cscott/3d-track60/roundabout-stl/roundabout-8-outer.stl

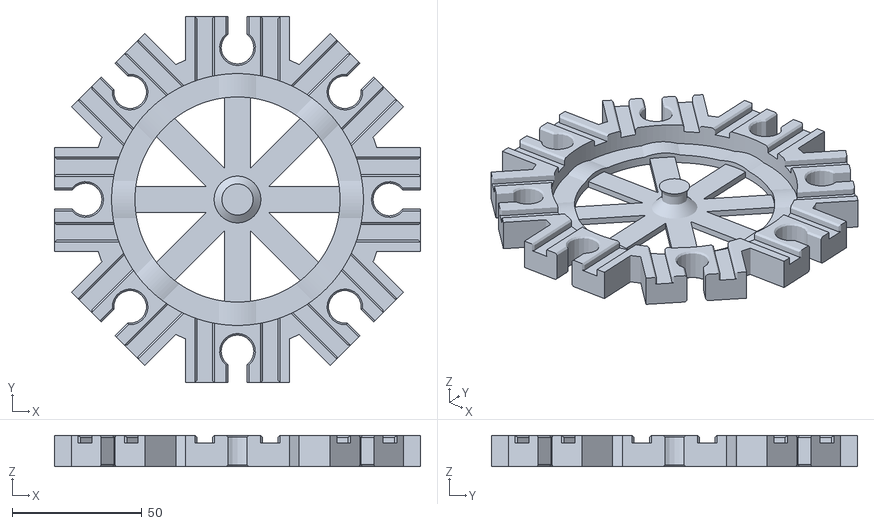
[picture p16: CAD file, 2017-08-04]
roundabout-stl/roundabout-8-outer.stl
141.0 x 141.0 x 12.0
