cscott/3d-track60/track60-stl/track60-name-BS==14.stl

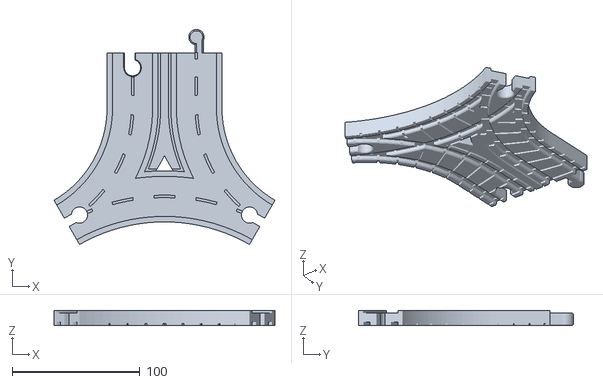
[picture p17: CAD file, 2017-12-13]
track60-stl/track60-name-BS==14.stl
173.1 x 168.4 x 12.0
