cscott/3d-track60/track60-swing-bridge-stl/track60-swing-bridge-swing-road-road-AT.stl

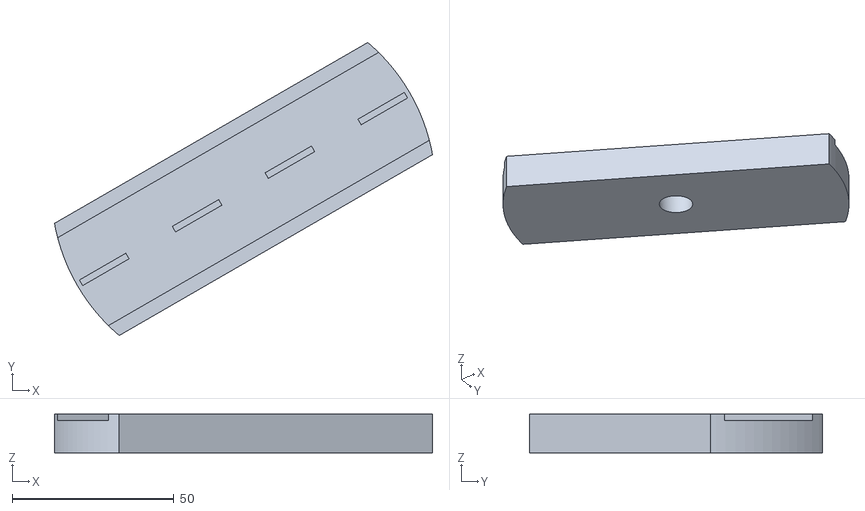
[picture p18: CAD file, 2017-11-13]
track60-swing-bridge-stl/track60-swing-bridge-swing-road-road-AT.stl
116.8 x 90.5 x 12.0
