cscott/3d-track60/track60-boat-stl/track60-boat-bottom.stl

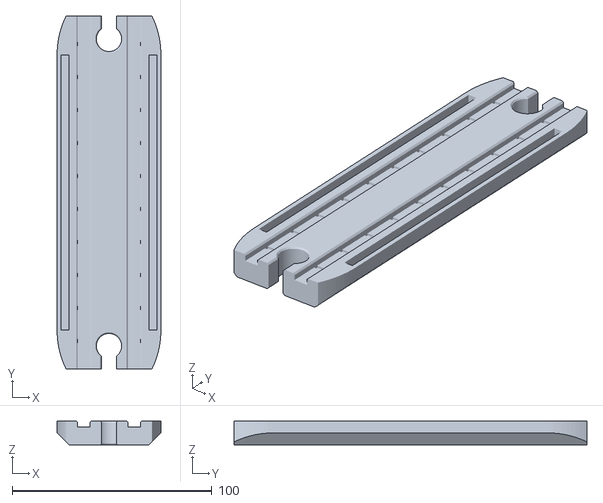
[picture p19: CAD file, 2017-08-04]
track60-boat-stl/track60-boat-bottom.stl
52.0 x 176.8 x 12.0
