cscott/3d-track60/track60-stl/track60-name-bt.stl

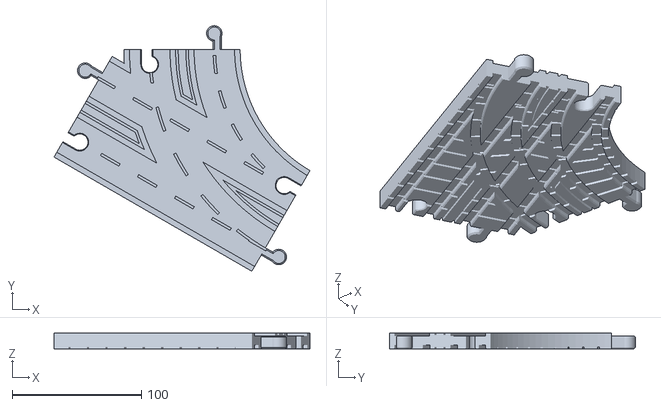
[picture p20: CAD file, 2017-12-13]
track60-stl/track60-name-bt.stl
198.1 x 190.1 x 12.0
