cscott/3d-track60/track60-swing-bridge-stl/track60-swing-bridge-base-road-road-ES.stl

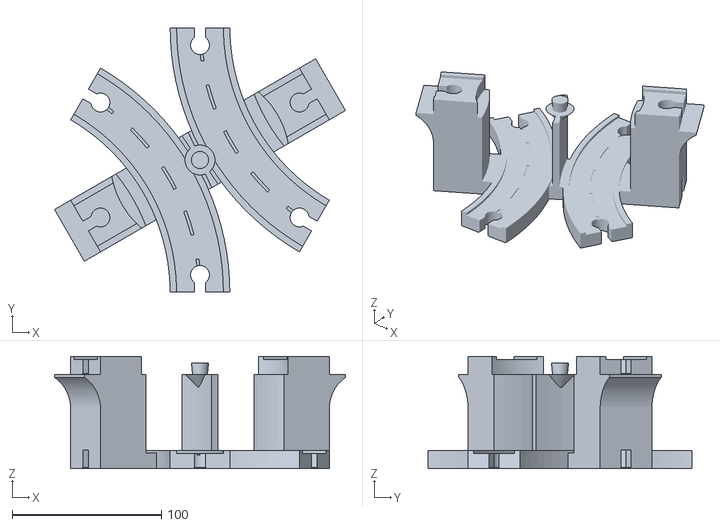
[picture p21: CAD file, 2017-11-13]
track60-swing-bridge-stl/track60-swing-bridge-base-road-road-ES.stl
194.8 x 176.8 x 75.0
