cscott/3d-track60/track60-stl/track60-name-bu.stl

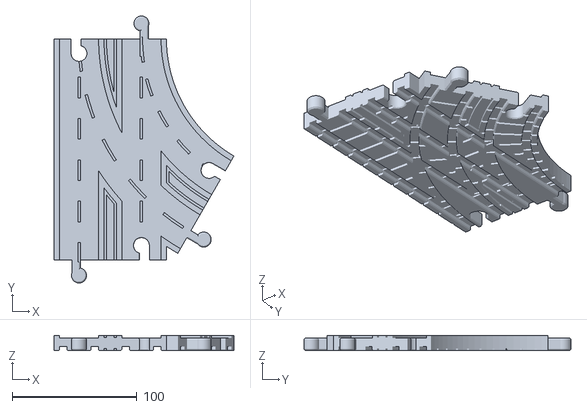
[picture p22: CAD file, 2017-12-13]
track60-stl/track60-name-bu.stl
144.1 x 213.8 x 12.0
