cscott/3d-track60/track60-swing-bridge-stl/track60-swing-bridge-base-road-road-AT.stl

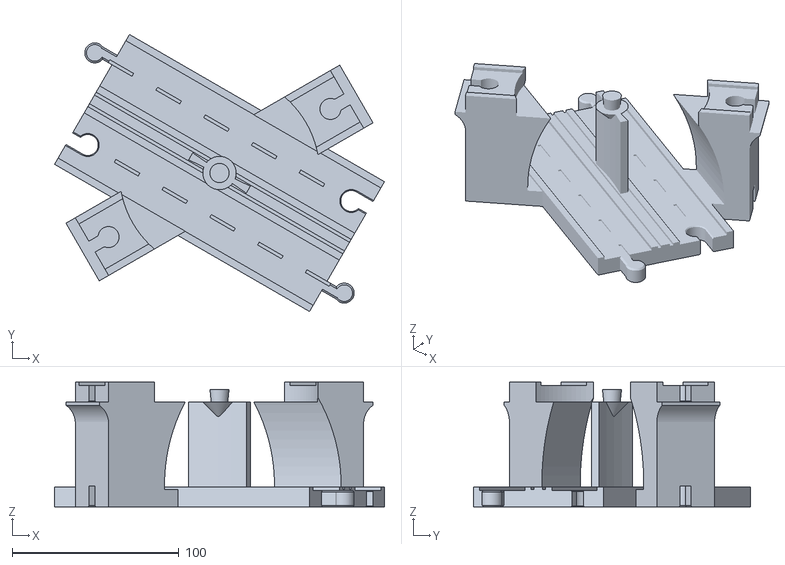
[picture p24: CAD file, 2017-11-13]
track60-swing-bridge-stl/track60-swing-bridge-base-road-road-AT.stl
198.1 x 166.4 x 75.0
