cscott/3d-track60/track60-stl/track60-dbl-roundabout-inner-straight-rail.stl

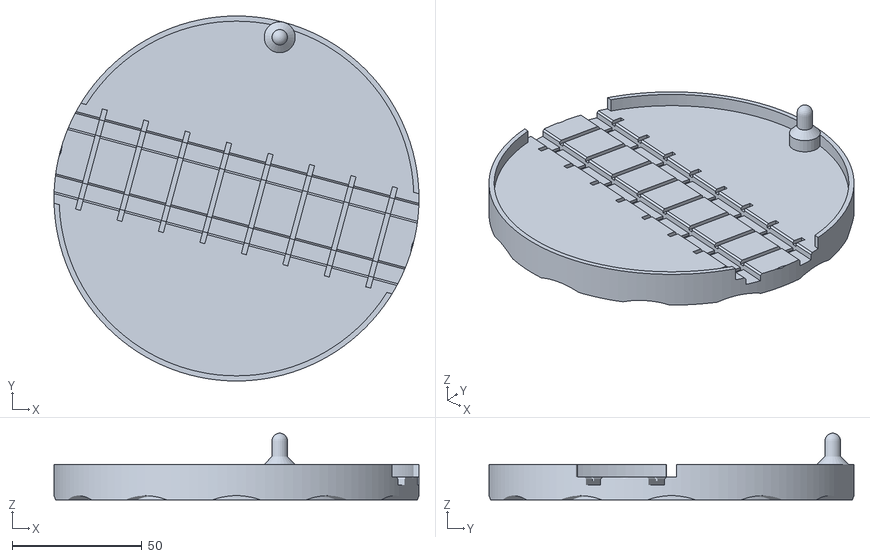
[picture p26: CAD file, 2017-12-12]
track60-stl/track60-dbl-roundabout-inner-straight-rail.stl
140.8 x 140.8 x 25.7
