cscott/3d-track60/track60-stl/track60-name-JS-6-road-blank.stl

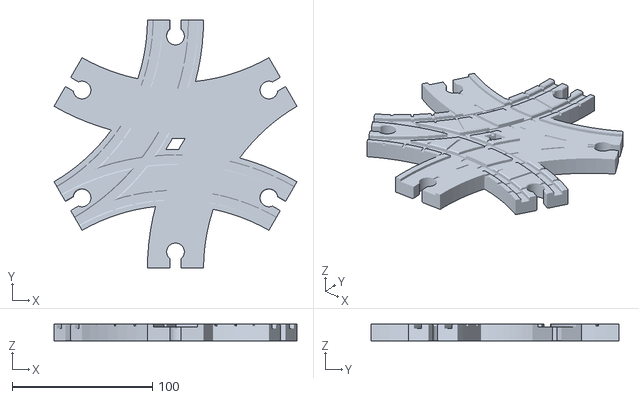
[picture p27: CAD file, 2017-12-12]
track60-stl/track60-name-JS-6-road-blank.stl
173.1 x 176.8 x 12.0
