cscott/3d-track60/track60-stl/track60-buffer-rail.stl

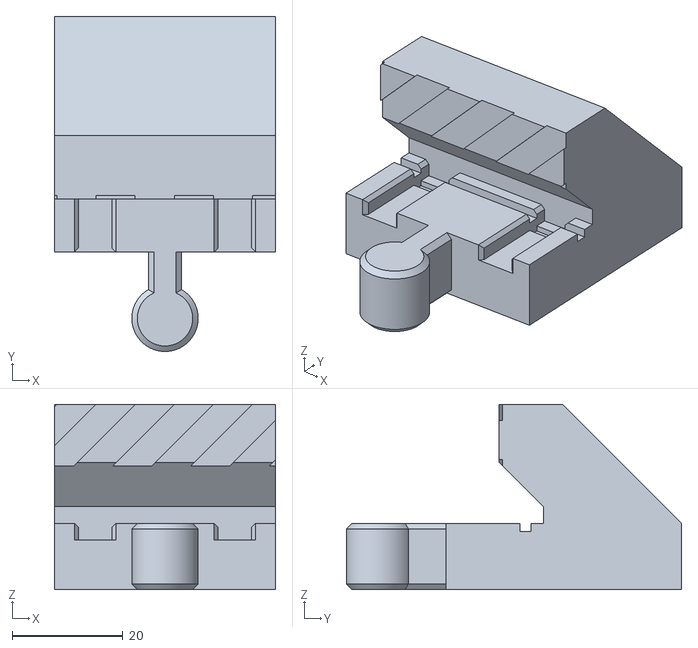
[picture p28: CAD file, 2017-12-11]
track60-stl/track60-buffer-rail.stl
40.0 x 60.6 x 33.5
