cscott/3d-track60/track60-swing-bridge-stl/track60-swing-bridge-base-rail-rail-AT.stl

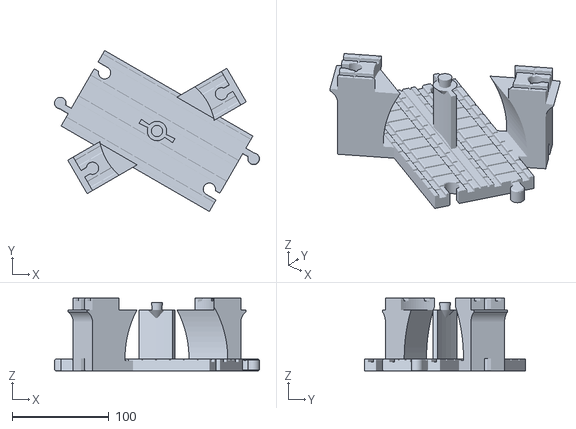
[picture p29: CAD file, 2017-11-13]
track60-swing-bridge-stl/track60-swing-bridge-base-rail-rail-AT.stl
211.8 x 166.4 x 75.0
