cscott/3d-track60/track60-stl/track60-buffer-road.stl

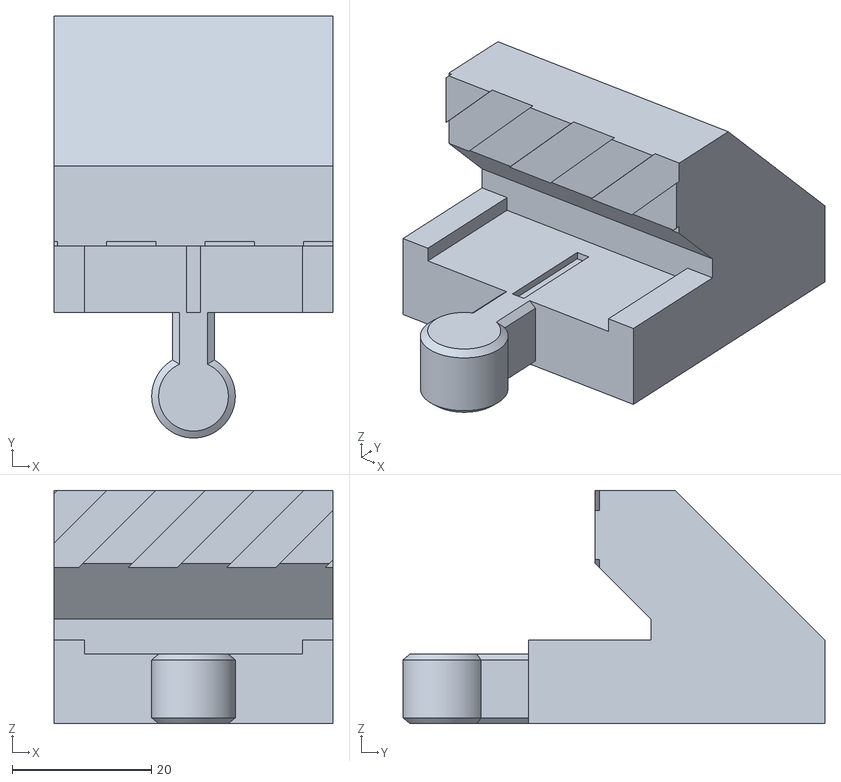
[picture p30: CAD file, 2017-12-11]
track60-stl/track60-buffer-road.stl
40.0 x 60.6 x 33.5
