cscott/3d-track60/track60-stl/track60-ramp-rail.stl

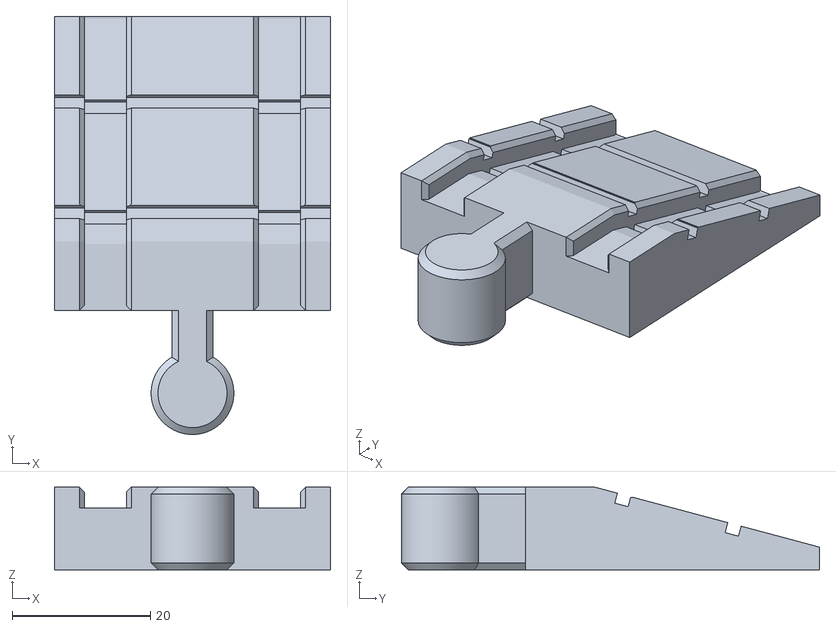
[picture p32: CAD file, 2017-12-11]
track60-stl/track60-ramp-rail.stl
40.0 x 60.6 x 12.0
