cscott/3d-track60/track60-stl/track60-pez2.stl

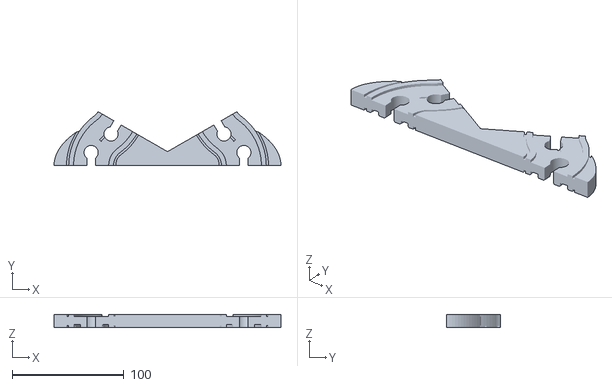
[picture p34: CAD file, 2017-11-12]
track60-stl/track60-pez2.stl
202.8 x 48.0 x 12.0
