cscott/3d-track60/track60-stl/track60-dbl-curve.stl

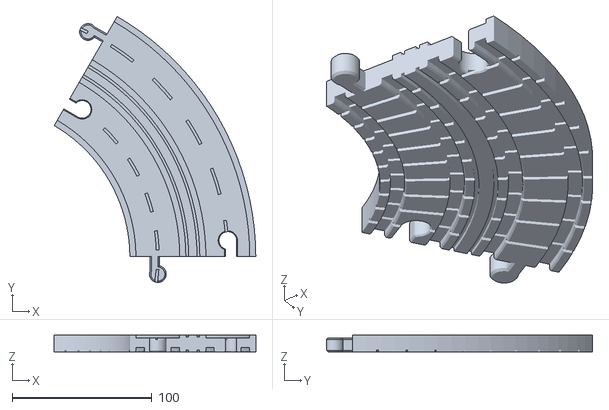
[picture p36: CAD file, 2017-08-04]
track60-stl/track60-dbl-curve.stl
144.1 x 190.1 x 12.0
