cscott/3d-track60/track60-stl/track60-curved-slope.stl

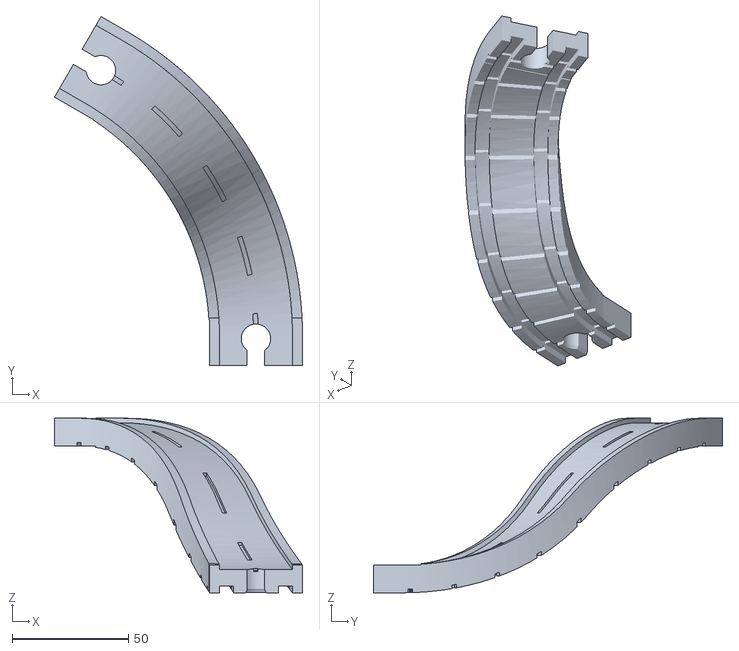
[picture p38: CAD file, 2017-08-04]
track60-stl/track60-curved-slope.stl
106.6 x 149.9 x 75.0
