cscott/3d-track60/track60-swing-bridge-stl/track60-swing-bridge-base-road-rail.stl

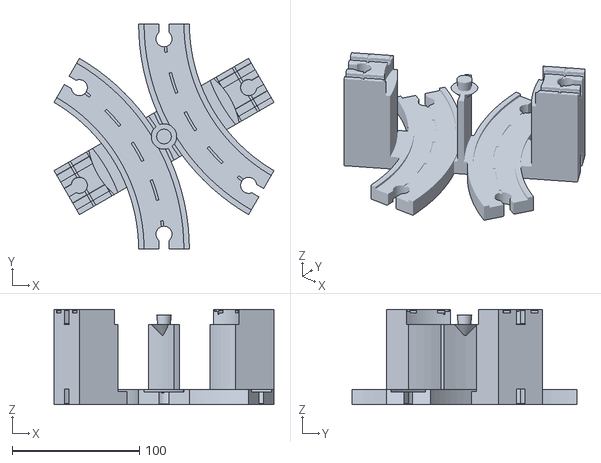
[picture p41: CAD file, 2017-08-04]
track60-swing-bridge-stl/track60-swing-bridge-base-road-rail.stl
173.1 x 176.8 x 75.0
