cscott/3d-track60/track60-stl/track60-switch6.stl

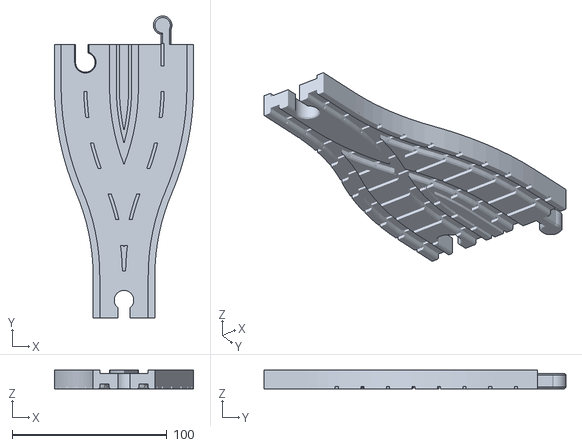
[picture p43: CAD file, 2017-08-04]
track60-stl/track60-switch6.stl
90.0 x 195.3 x 12.0
