cscott/3d-track60/track60-stl/track60-recycling-left.stl

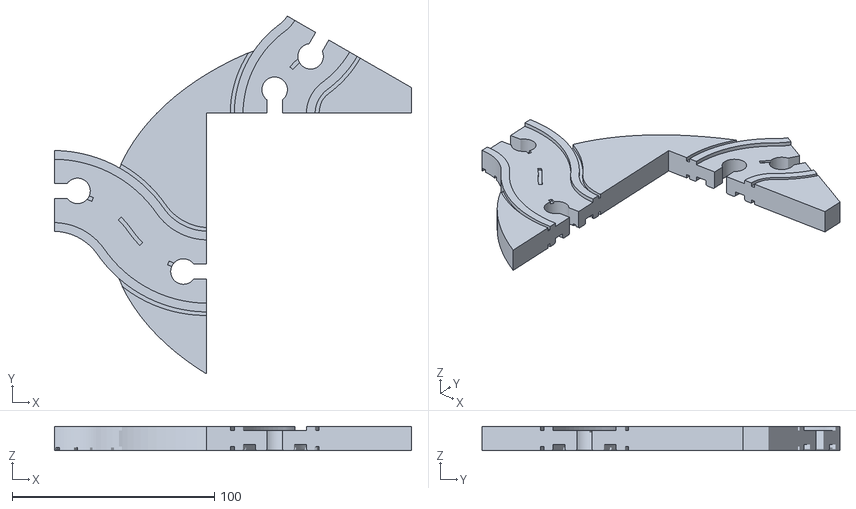
[picture p44: CAD file, 2017-08-04]
track60-stl/track60-recycling-left.stl
176.9 x 177.2 x 12.0
