cscott/3d-track60/track60-stl/track60-roundabout-inner-crossing4-rail.stl

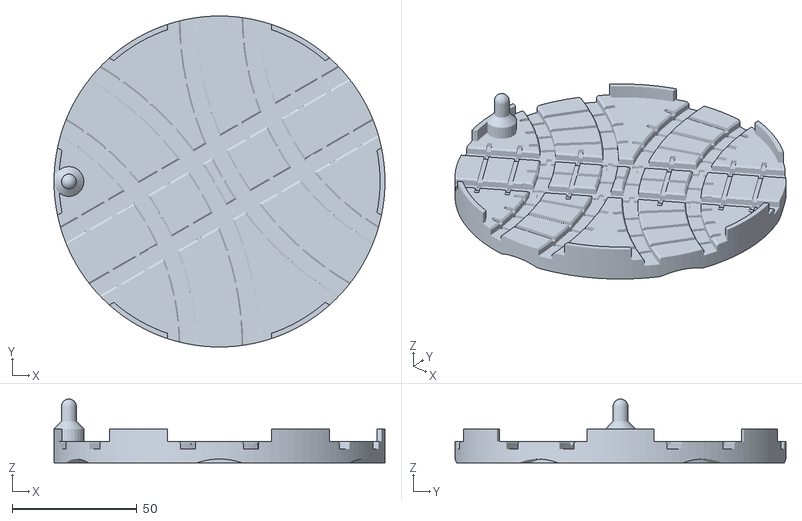
[picture p46: CAD file, 2017-08-04]
track60-stl/track60-roundabout-inner-crossing4-rail.stl
132.8 x 132.8 x 25.7
