cscott/3d-track60/track60-stl/track60-crossing5.stl

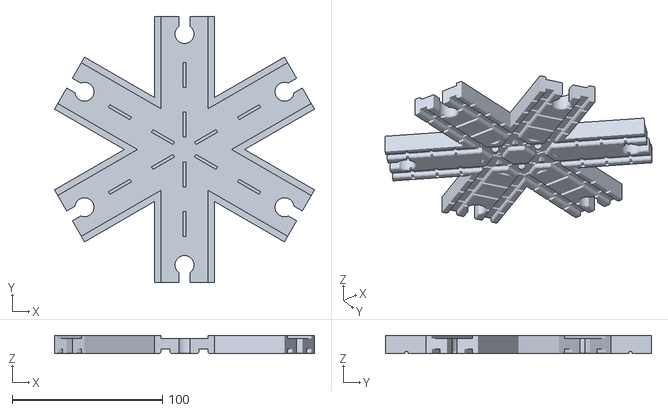
[picture p47: CAD file, 2017-08-04]
track60-stl/track60-crossing5.stl
173.1 x 176.8 x 12.0
