cscott/3d-track60/track60-stl/track60-roundabout-inner-straight-road.stl

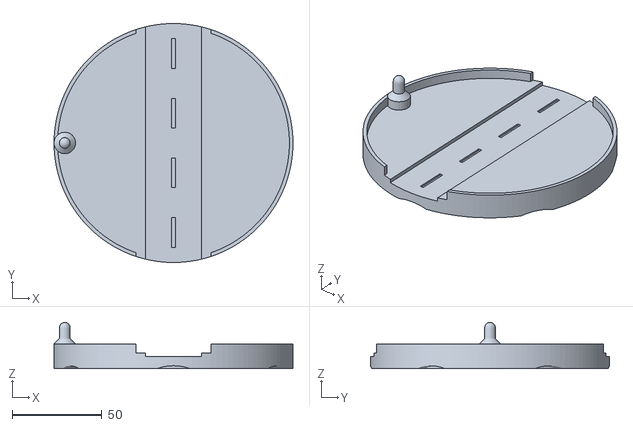
[picture p50: CAD file, 2017-08-04]
track60-stl/track60-roundabout-inner-straight-road.stl
132.8 x 132.8 x 25.7
