cscott/3d-track60/track60-stl/track60-switch12-rail.stl

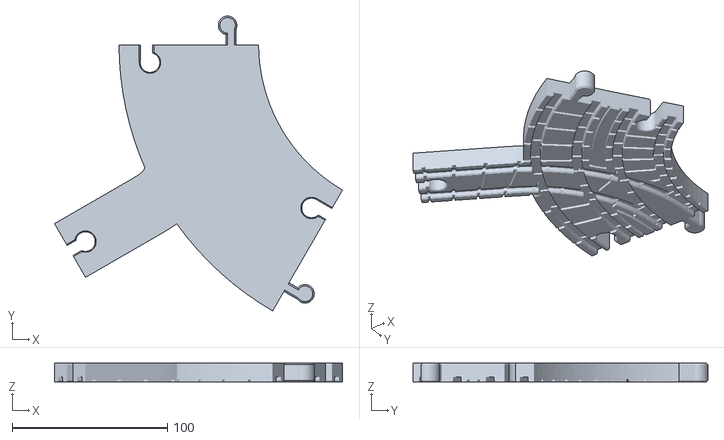
[picture p52: CAD file, 2017-08-04]
track60-stl/track60-switch12-rail.stl
185.6 x 190.1 x 12.0
