cscott/3d-track60/track60-stl/track60-roundabout-inner-straight-rail.stl

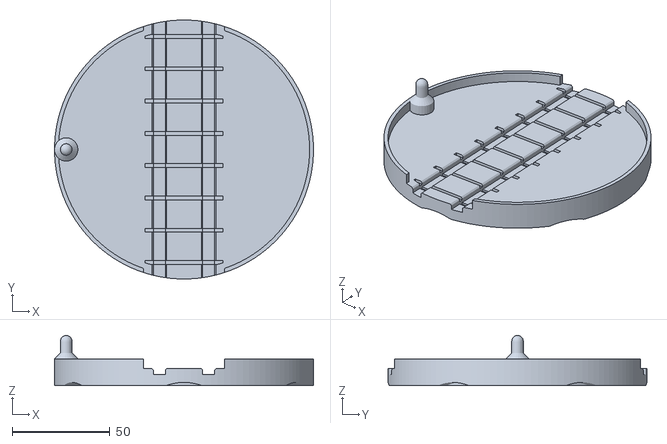
[picture p53: CAD file, 2017-08-04]
track60-stl/track60-roundabout-inner-straight-rail.stl
132.8 x 132.8 x 25.7
