cscott/3d-track60/track60-stl/track60-crossing7-rail.stl

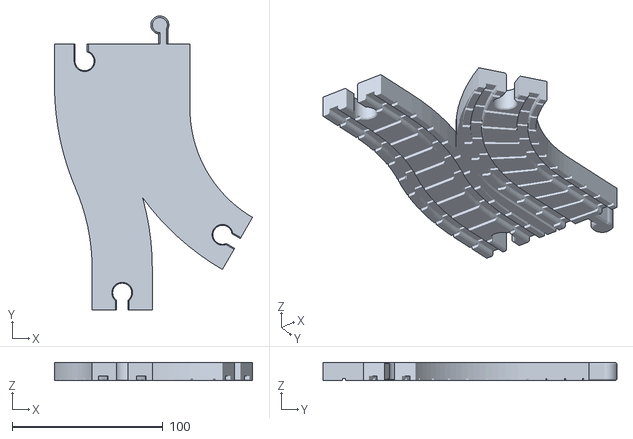
[picture p55: CAD file, 2017-08-04]
track60-stl/track60-crossing7-rail.stl
131.6 x 195.3 x 12.0
