cscott/3d-track60/track60-stl/track60-mcdonalds-bottom-road-blank.stl

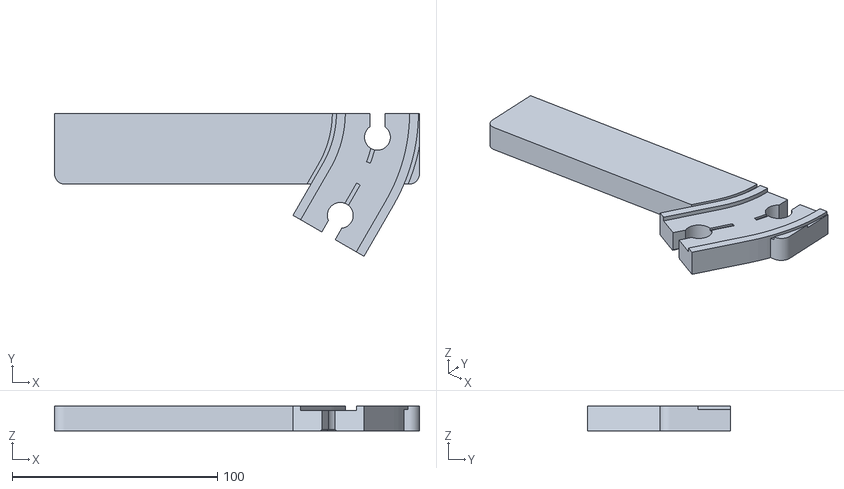
[picture p57: CAD file, 2017-08-04]
track60-stl/track60-mcdonalds-bottom-road-blank.stl
178.0 x 69.6 x 12.0
