cscott/3d-track60/track60-stl/track60-switch1-road.stl

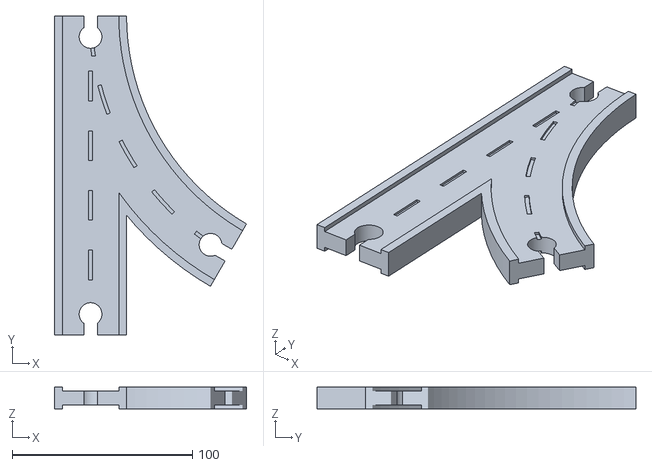
[picture p58: CAD file, 2017-08-04]
track60-stl/track60-switch1-road.stl
106.6 x 176.8 x 12.0
