cscott/3d-track60/track60-stl/track60-switch4.stl

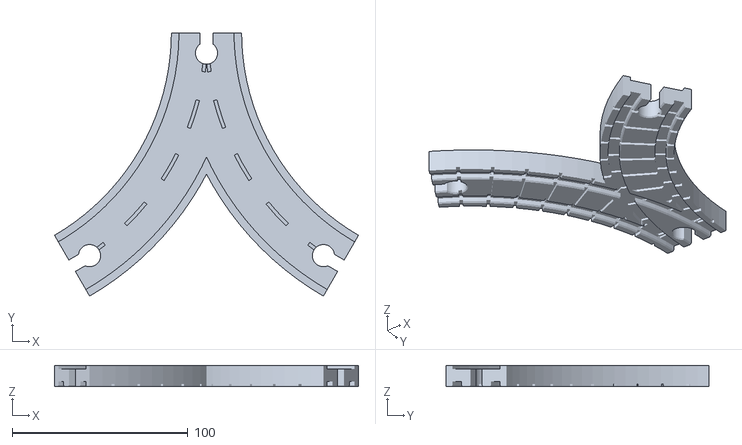
[picture p60: CAD file, 2017-08-04]
track60-stl/track60-switch4.stl
173.1 x 149.9 x 12.0
