cscott/3d-track60/track60-stl/track60-switch1-rail.stl

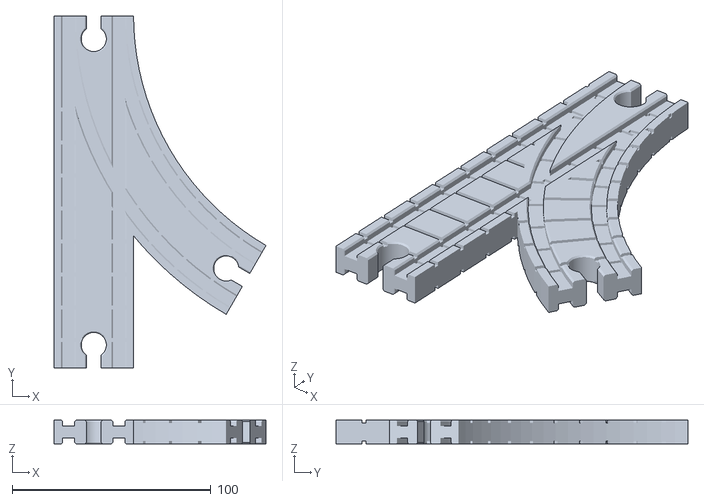
[picture p61: CAD file, 2017-08-04]
track60-stl/track60-switch1-rail.stl
106.6 x 176.8 x 12.0
