cscott/3d-track60/track60-stl/track60-switch13-right.stl

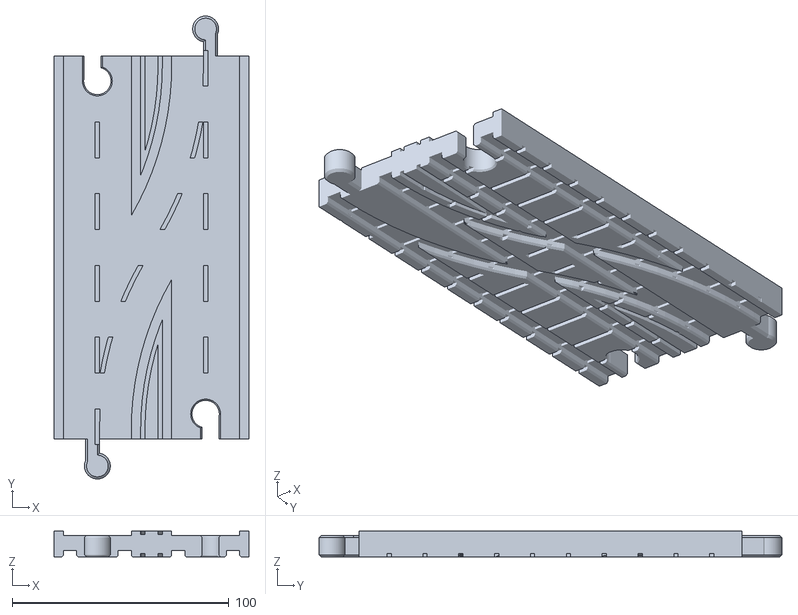
[picture p62: CAD file, 2017-08-04]
track60-stl/track60-switch13-right.stl
90.0 x 213.8 x 12.0
