cscott/3d-track60/track60-stl/track60-switch3-road.stl

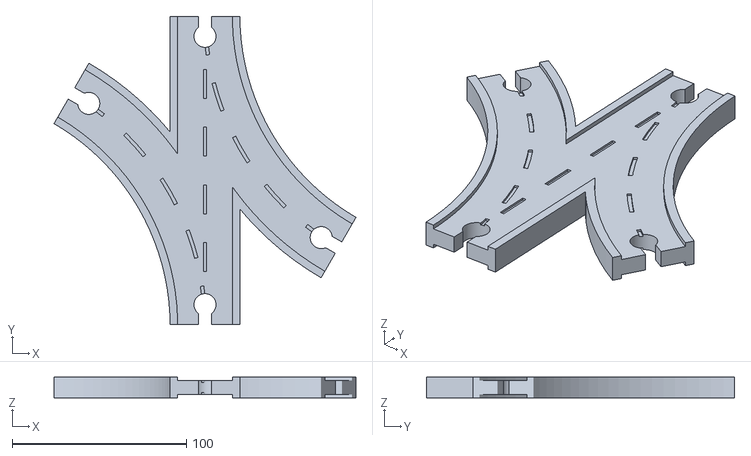
[picture p64: CAD file, 2017-08-04]
track60-stl/track60-switch3-road.stl
173.1 x 176.8 x 12.0
