cscott/3d-track60/track60-stl/track60-post-office-road-blank.stl

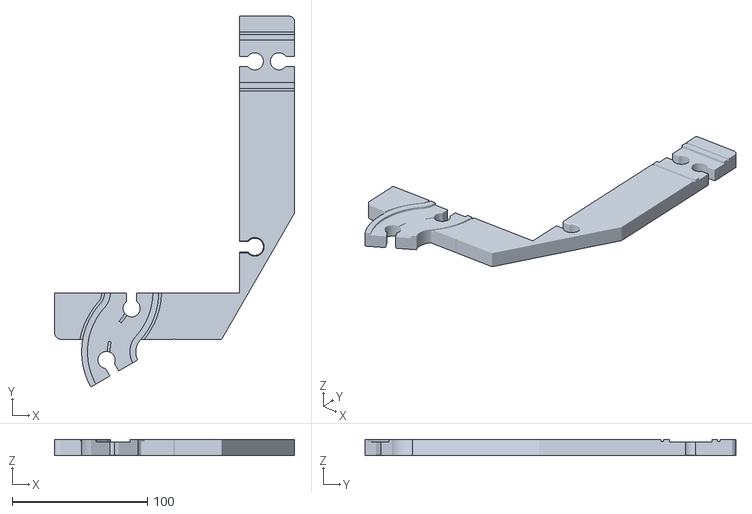
[picture p65: CAD file, 2017-08-04]
track60-stl/track60-post-office-road-blank.stl
177.3 x 274.1 x 12.0
