cscott/3d-track60/track60-stl/track60-mcdonalds-top-road-blank.stl

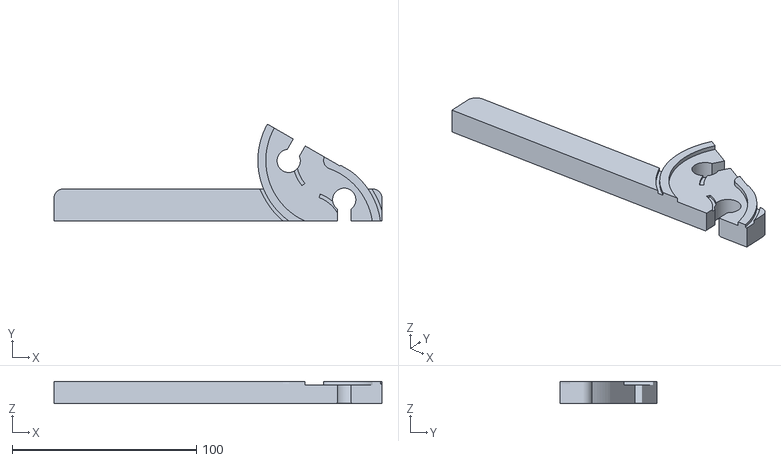
[picture p67: CAD file, 2017-08-04]
track60-stl/track60-mcdonalds-top-road-blank.stl
178.0 x 52.6 x 12.0
