cscott/3d-track60/track60-stl/track60-thomas-crossing.stl

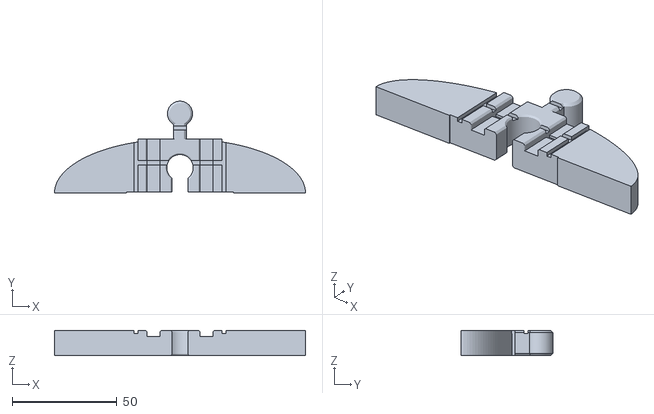
[picture p69: CAD file, 2017-08-04]
track60-stl/track60-thomas-crossing.stl
120.0 x 43.8 x 12.0
