cscott/3d-track60/track60-stl/track60-crossing10.stl

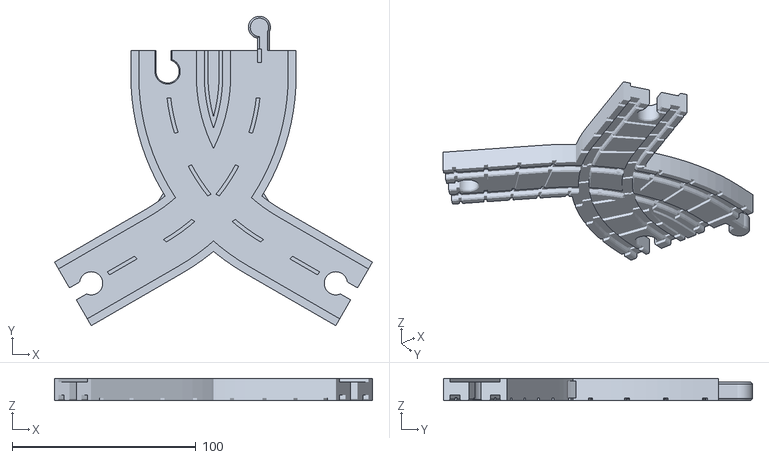
[picture p70: CAD file, 2017-08-04]
track60-stl/track60-crossing10.stl
173.1 x 168.4 x 12.0
