cscott/3d-track60/track60-stl/track60-misc3.stl

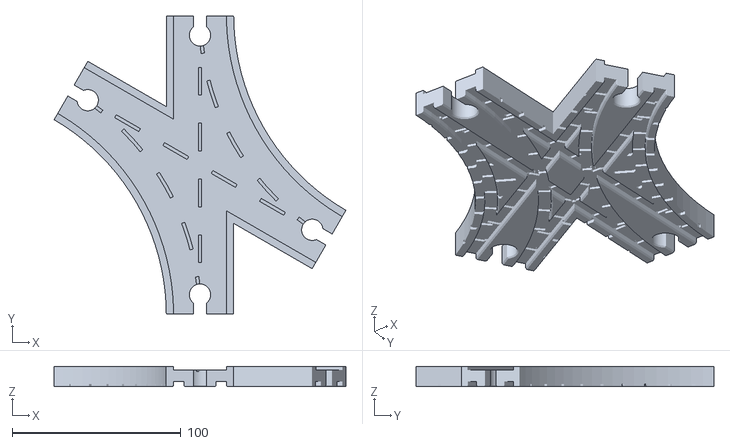
[picture p71: CAD file, 2017-08-04]
track60-stl/track60-misc3.stl
173.1 x 176.8 x 12.0
