cscott/3d-track60/track60-stl/track60-gas-station-left.stl

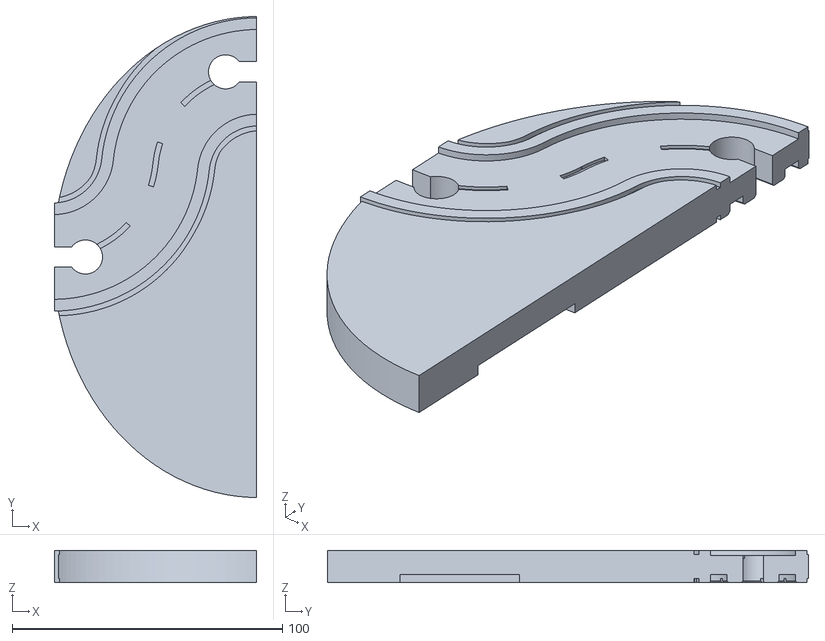
[picture p75: CAD file, 2017-08-04]
track60-stl/track60-gas-station-left.stl
74.8 x 178.0 x 12.0
