cscott/3d-track60/track60-stl/track60-switch14-rail.stl

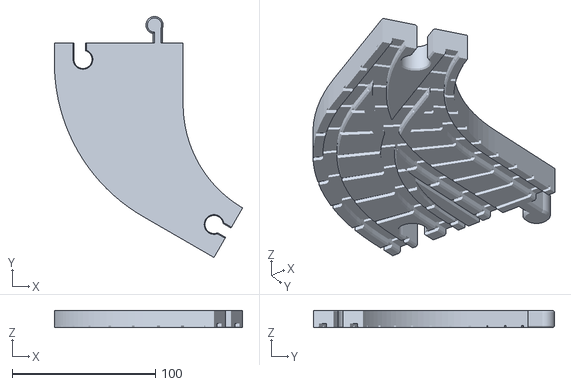
[picture p76: CAD file, 2017-08-04]
track60-stl/track60-switch14-rail.stl
131.6 x 168.4 x 12.0
