cscott/3d-track60/track60-stl/track60-post-office-bottom-road-blank.stl

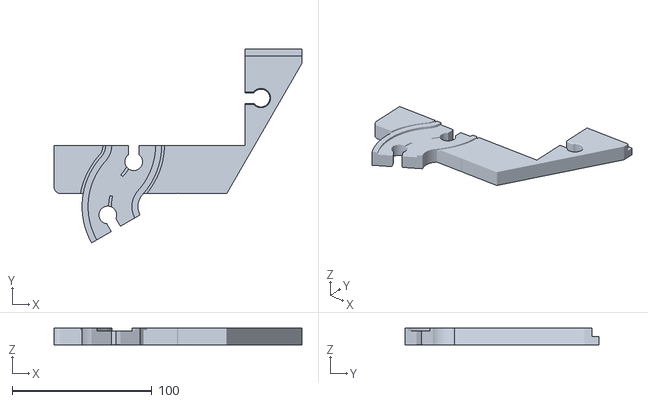
[picture p77: CAD file, 2017-08-04]
track60-stl/track60-post-office-bottom-road-blank.stl
177.3 x 138.6 x 12.0
