cscott/3d-track60/track60-stl/track60-crossing8-right.stl

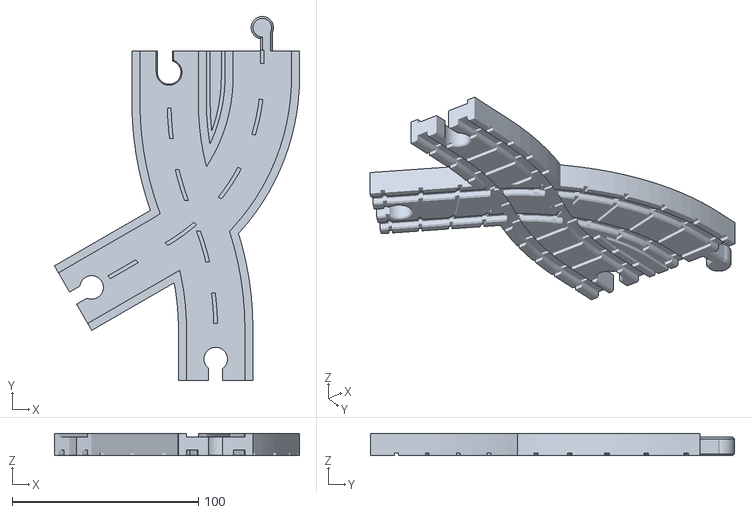
[picture p78: CAD file, 2017-08-04]
track60-stl/track60-crossing8-right.stl
131.6 x 195.3 x 12.0
