cscott/3d-track60/track60-stl/track60-crossing6.stl

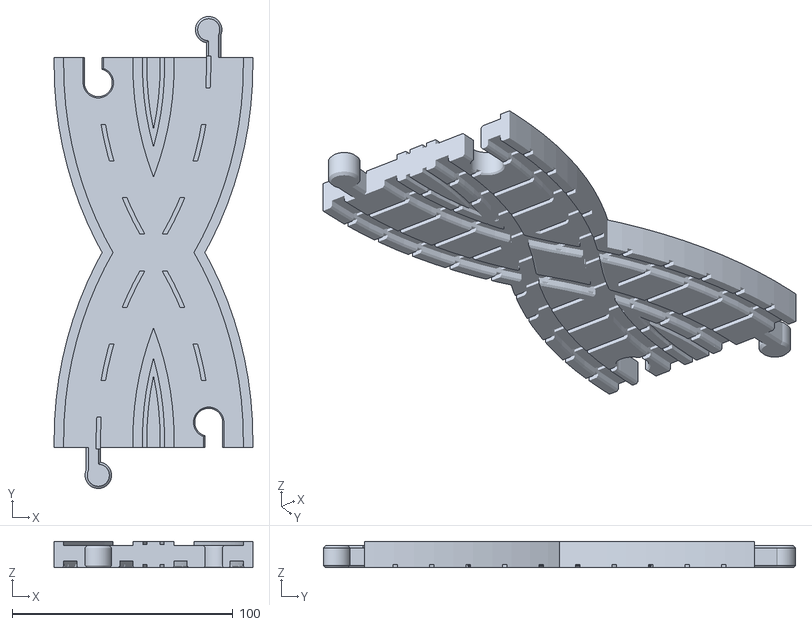
[picture p79: CAD file, 2017-08-04]
track60-stl/track60-crossing6.stl
90.0 x 213.8 x 12.0
