cscott/3d-track60/track60-stl/track60-crossing8-road.stl

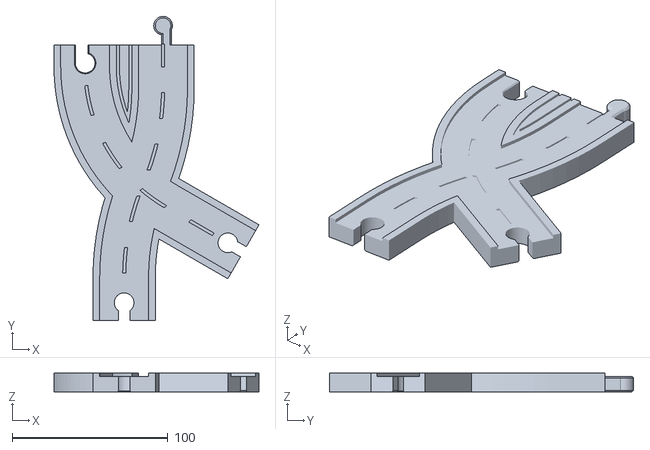
[picture p80: CAD file, 2017-08-04]
track60-stl/track60-crossing8-road.stl
131.6 x 195.3 x 12.0
