cscott/3d-track60/track60-stl/track60-switch1-left.stl

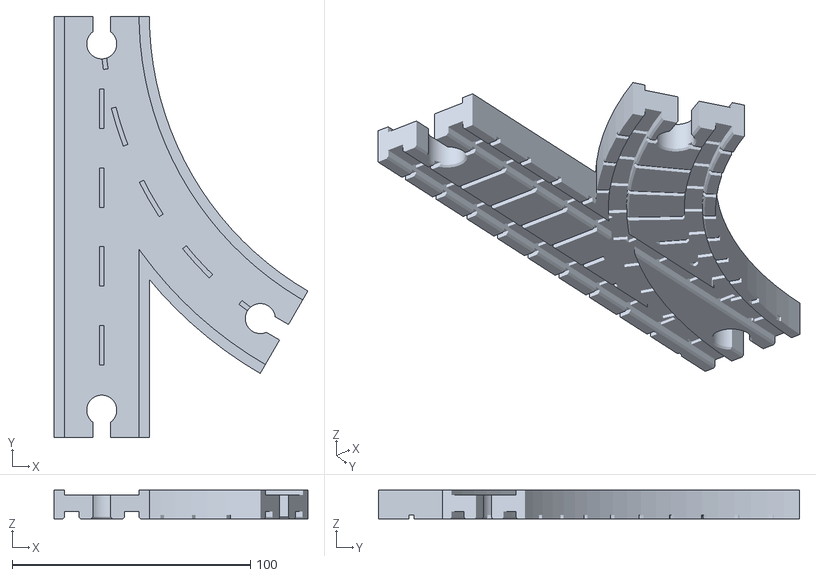
[picture p81: CAD file, 2017-08-04]
track60-stl/track60-switch1-left.stl
106.6 x 176.8 x 12.0
