cscott/3d-track60/track60-stl/track60-switch16-right.stl

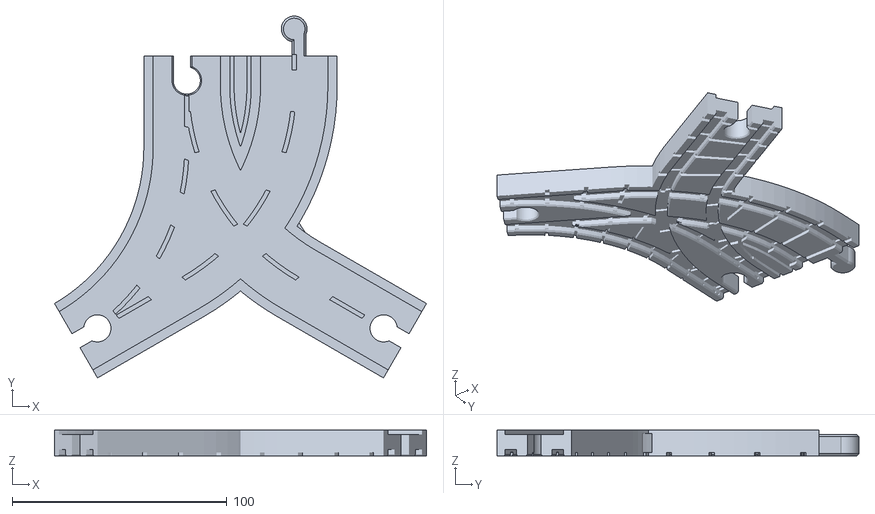
[picture p82: CAD file, 2017-08-04]
track60-stl/track60-switch16-right.stl
173.1 x 168.4 x 12.0
