cscott/3d-track60/track60-stl/track60-switch1-right.stl

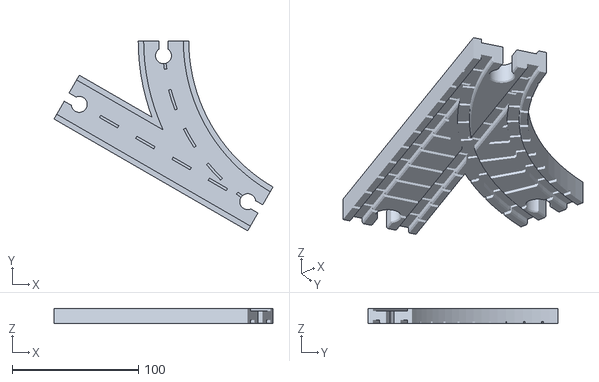
[picture p85: CAD file, 2017-08-04]
track60-stl/track60-switch1-right.stl
173.1 x 149.9 x 12.0
