cscott/3d-track60/track60-stl/track60-misc4.stl

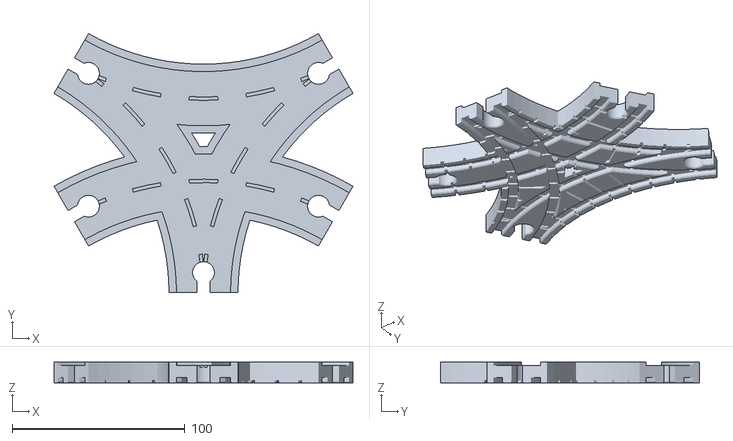
[picture p86: CAD file, 2017-08-04]
track60-stl/track60-misc4.stl
173.1 x 149.9 x 12.0
