cscott/3d-track60/track60-stl/track60-big-slope.stl

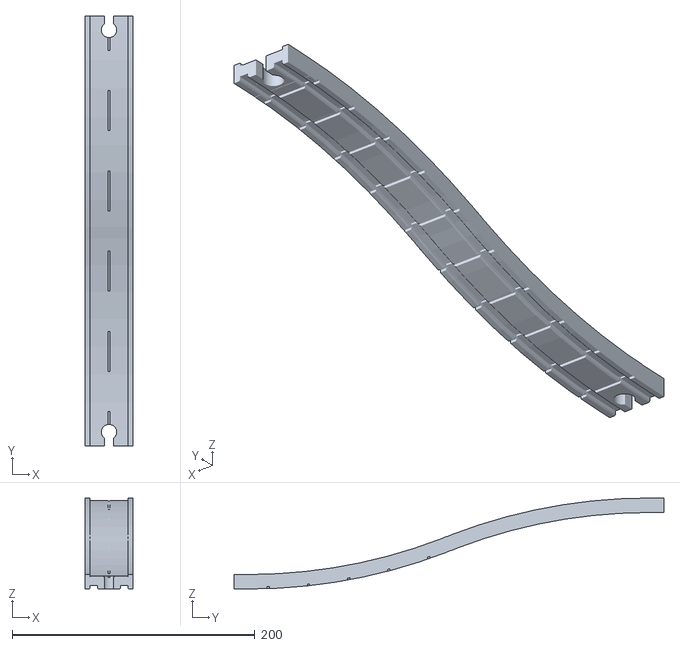
[picture p88: CAD file, 2017-08-04]
track60-stl/track60-big-slope.stl
40.0 x 354.6 x 75.0
