cscott/3d-track60/track60-stl/track60-half-straight.stl

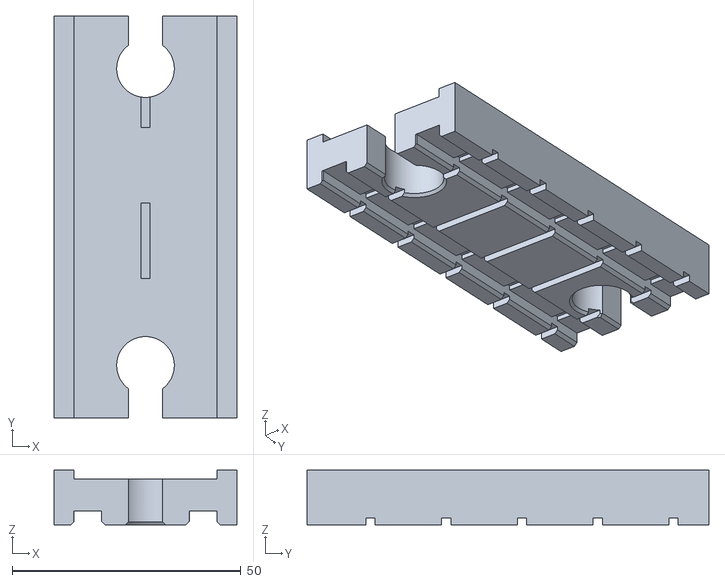
[picture p89: CAD file, 2017-08-04]
track60-stl/track60-half-straight.stl
40.0 x 87.9 x 12.0
