cscott/3d-track60/track60-stl/track60-roundabout-road.stl

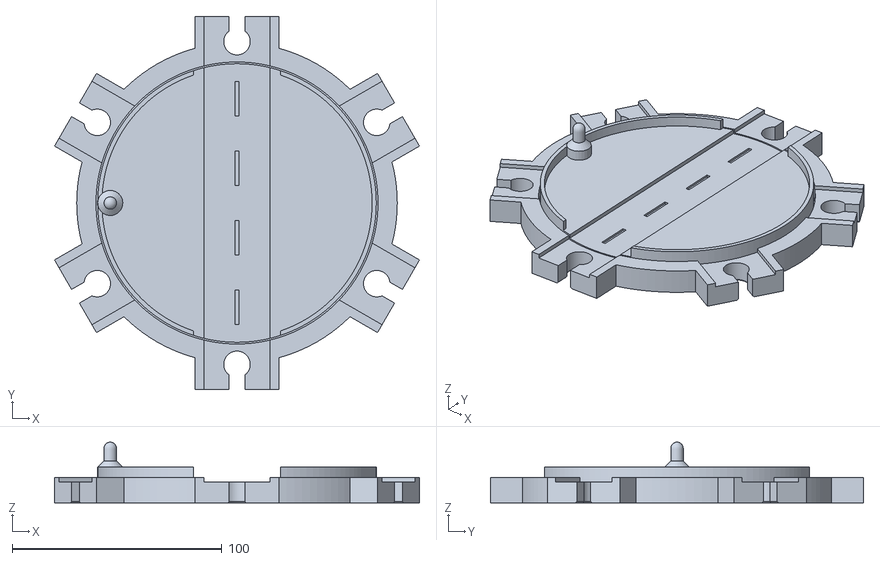
[picture p91: CAD file, 2017-08-04]
track60-stl/track60-roundabout-road.stl
174.0 x 177.8 x 29.0
