cscott/3d-track60/track60-stl/track60-dbl-ramp-road.stl

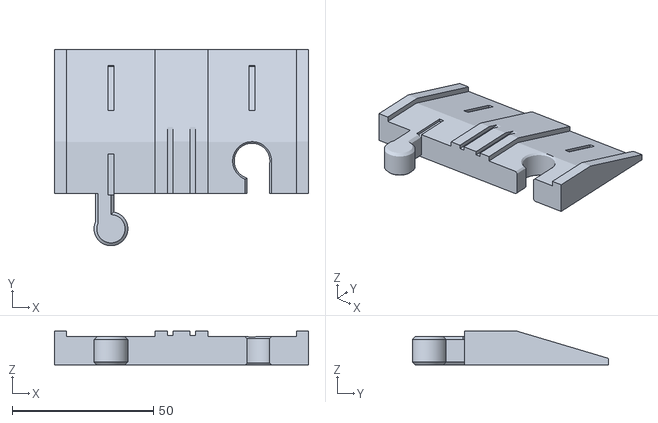
[picture p95: CAD file, 2017-08-04]
track60-stl/track60-dbl-ramp-road.stl
90.0 x 69.6 x 12.0
