cscott/3d-track60/track60-stl/track60-name-atAV-1.stl

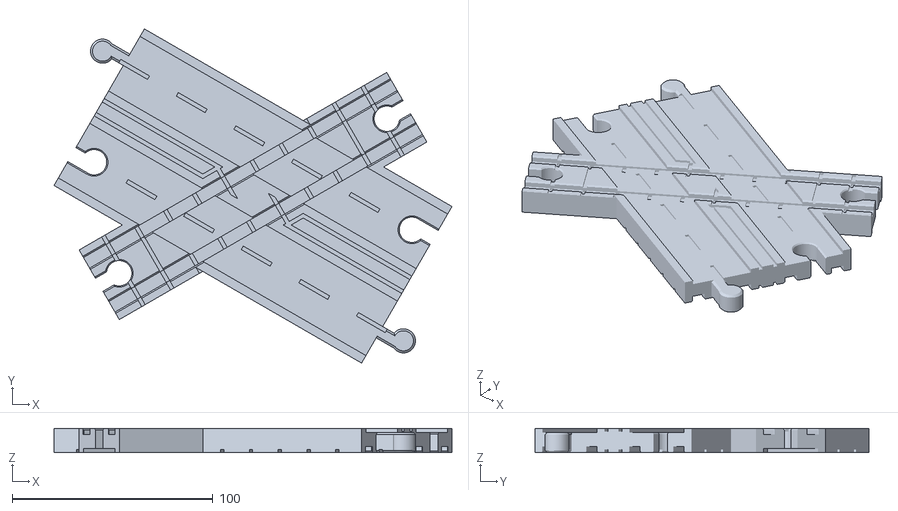
[picture p96: CAD file, 2017-08-04]
track60-stl/track60-name-atAV-1.stl
198.1 x 166.4 x 12.0
