cscott/3d-track60/track60-stl/track60-curved-slope-with-base-rail.stl

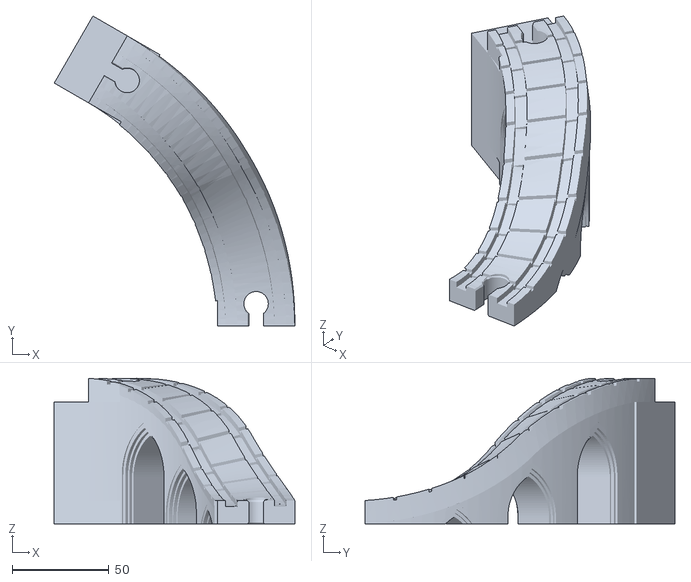
[picture p97: CAD file, 2017-08-04]
track60-stl/track60-curved-slope-with-base-rail.stl
124.3 x 160.2 x 75.2
