cscott/3d-track60/track60-stl/track60-slope-rail.stl

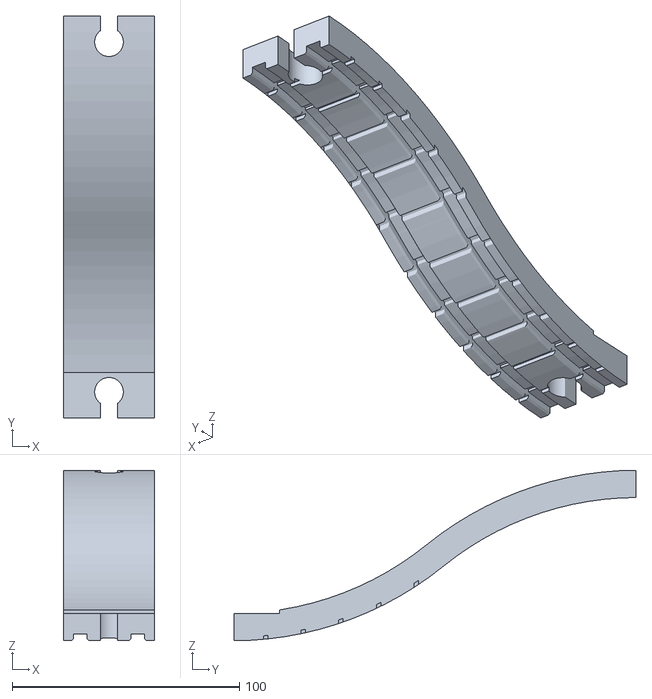
[picture p98: CAD file, 2017-08-04]
track60-stl/track60-slope-rail.stl
40.0 x 176.8 x 75.0
