cscott/3d-track60/track60-stl/track60-name-CS-1-rail.stl

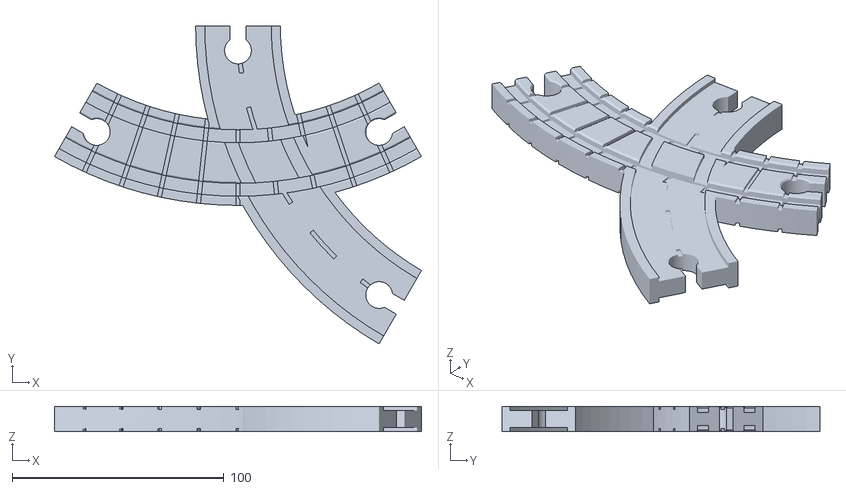
[picture p99: CAD file, 2017-08-04]
track60-stl/track60-name-CS-1-rail.stl
173.1 x 149.9 x 12.0
