cscott/3d-track60/track60-stl/track60-switch7-left.stl

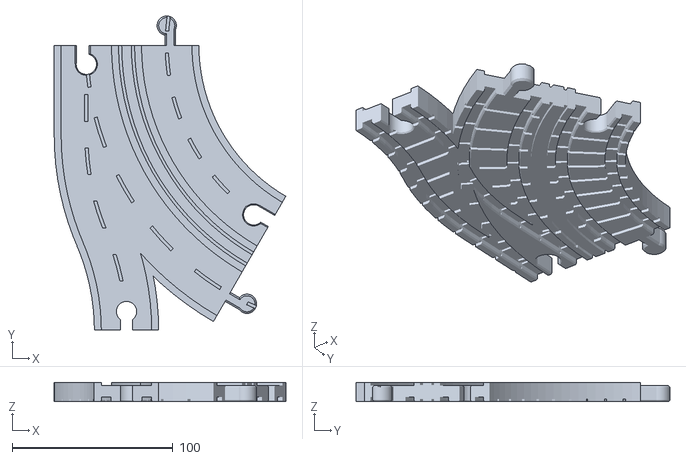
[picture p100: CAD file, 2017-08-04]
track60-stl/track60-switch7-left.stl
144.1 x 195.3 x 12.0
