cscott/3d-track60/track60-stl/track60-dogbone.stl

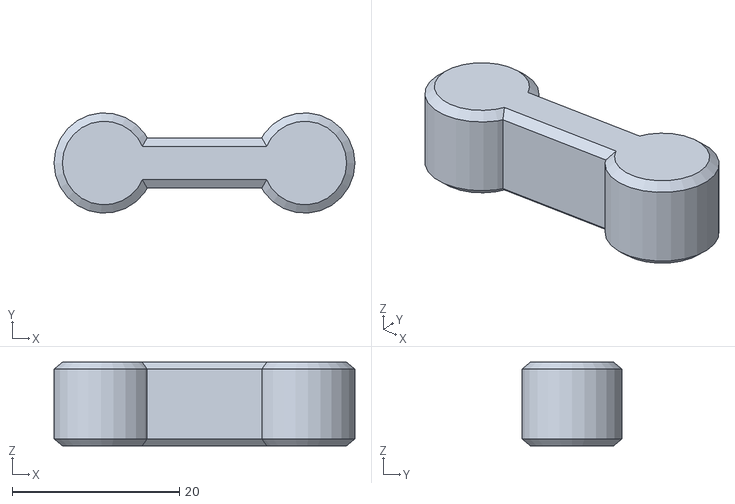
[picture p103: CAD file, 2017-08-04]
track60-stl/track60-dogbone.stl
36.0 x 12.0 x 10.0
