cscott/3d-track60/track60-stl/track60-riser.stl

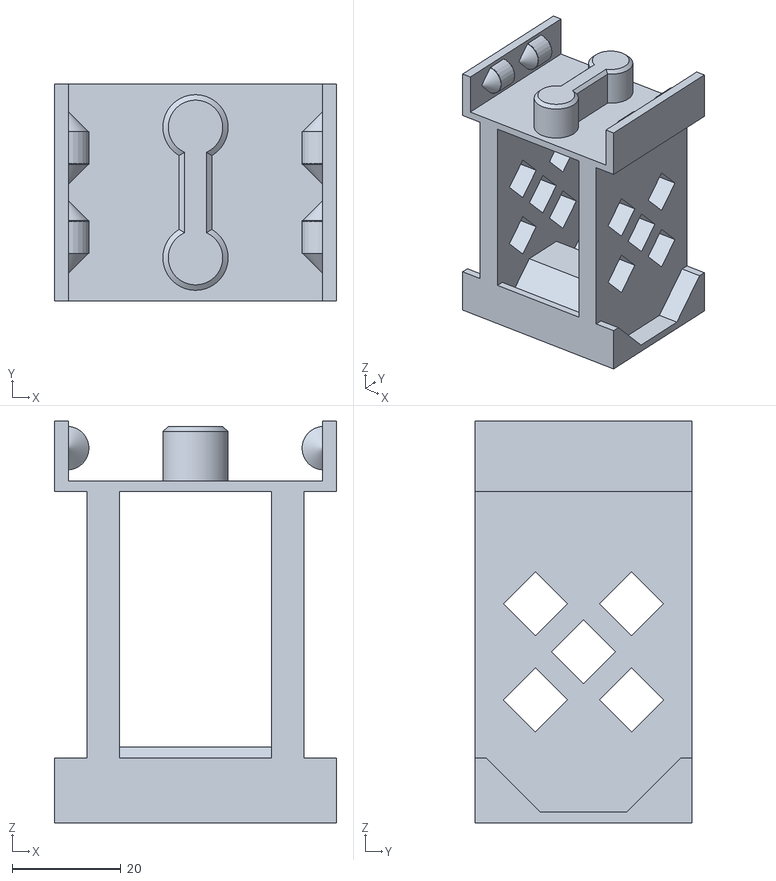
[picture p104: CAD file, 2017-08-04]
track60-stl/track60-riser.stl
52.0 x 40.0 x 74.0
