cscott/3d-track60/track60-stl/track60-curve.stl

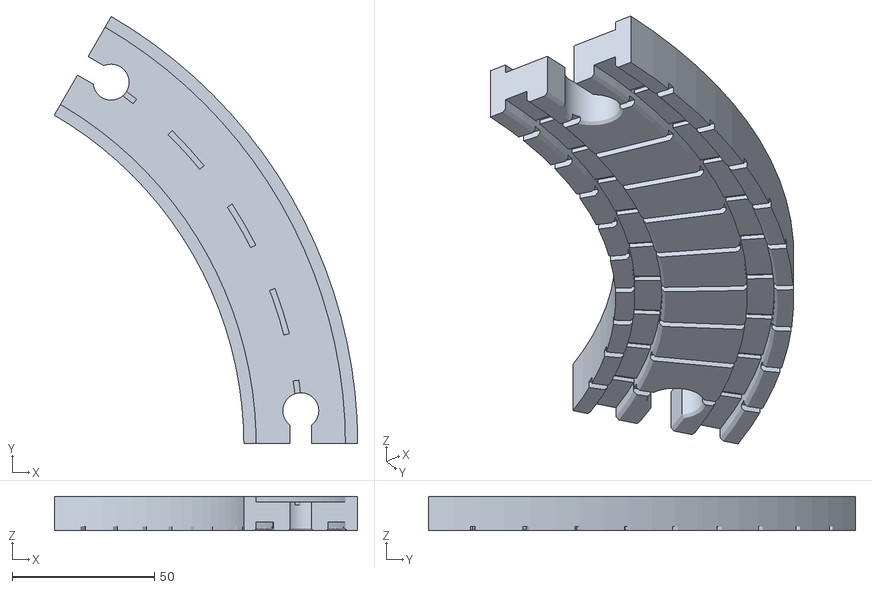
[picture p105: CAD file, 2017-08-04]
track60-stl/track60-curve.stl
106.6 x 149.9 x 12.0
