cscott/3d-track60/track60-stl/track60-dbl-buffer-road.stl

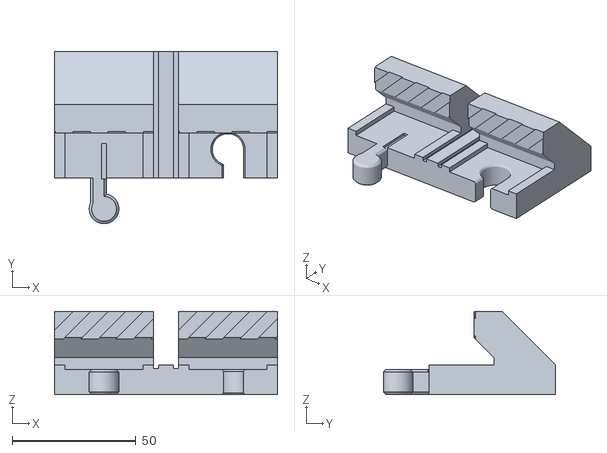
[picture p106: CAD file, 2017-08-04]
track60-stl/track60-dbl-buffer-road.stl
90.0 x 69.6 x 33.5
