cscott/3d-track60/track60-stl/track60-switch10-rail.stl

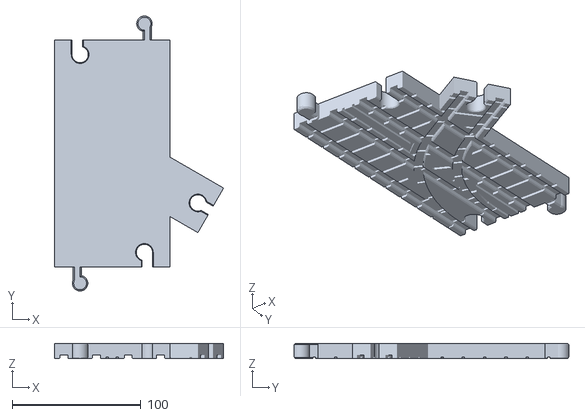
[picture p107: CAD file, 2017-08-04]
track60-stl/track60-switch10-rail.stl
131.6 x 213.8 x 12.0
