cscott/3d-track60/track60-stl/track60-firehouse.stl

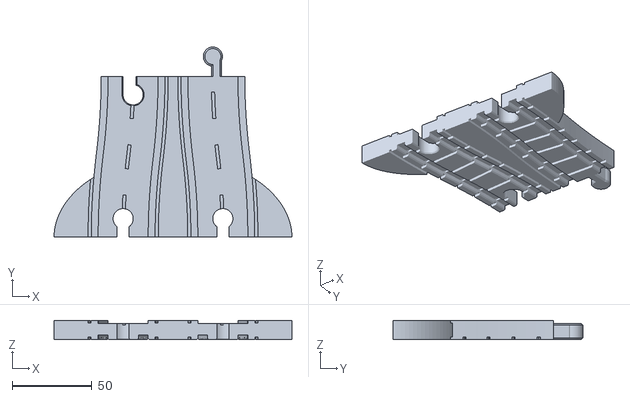
[picture p108: CAD file, 2017-08-04]
track60-stl/track60-firehouse.stl
149.2 x 119.1 x 12.0
