cscott/3d-track60/track60-stl/track60-straight.stl

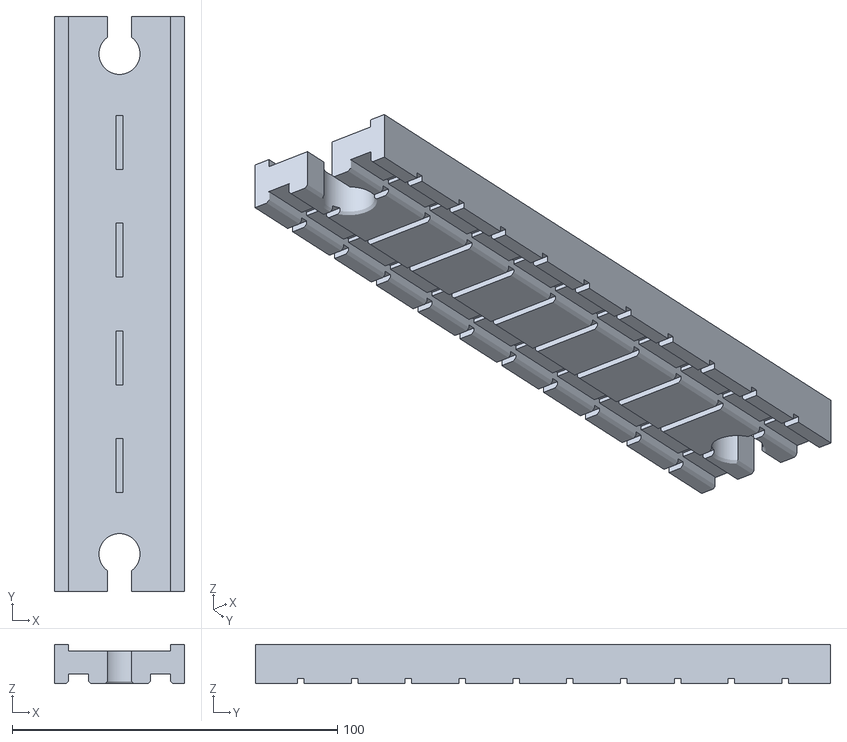
[picture p109: CAD file, 2017-08-04]
track60-stl/track60-straight.stl
40.0 x 176.8 x 12.0
