cscott/3d-track60/track60-stl/track60-big-curved-slope.stl

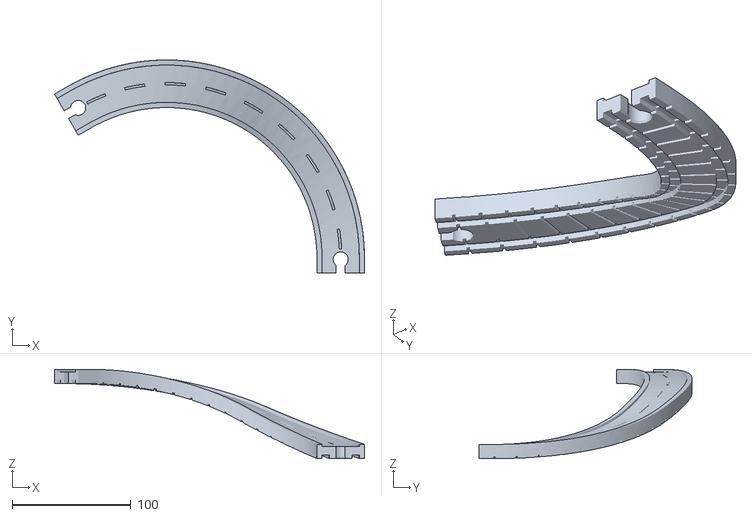
[picture p110: CAD file, 2017-08-04]
track60-stl/track60-big-curved-slope.stl
260.6 x 179.1 x 75.0
