cscott/3d-track60/track60-stl/track60-post-office-top-road-blank.stl

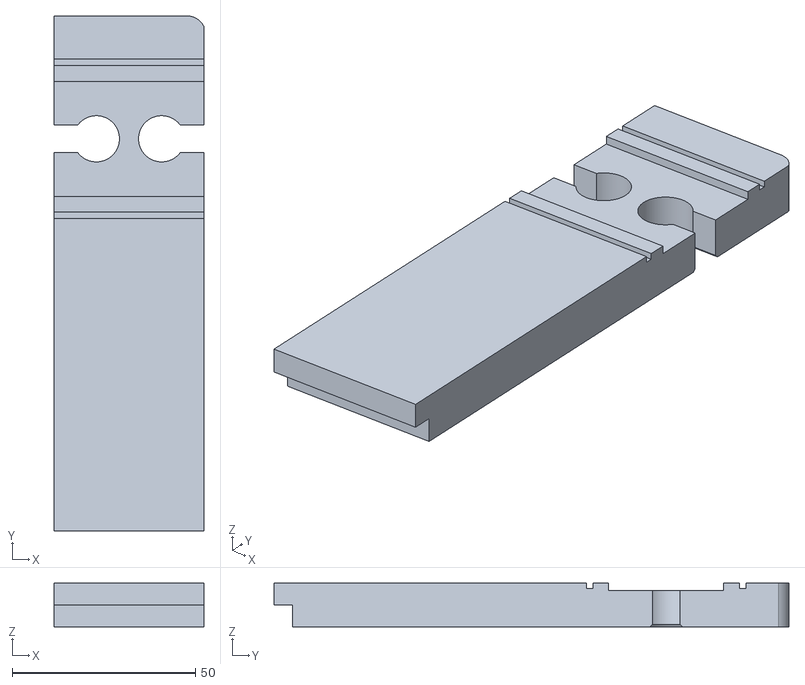
[picture p111: CAD file, 2017-08-04]
track60-stl/track60-post-office-top-road-blank.stl
40.8 x 140.5 x 12.0
