cscott/3d-track60/track60-stl/track60-switch11-rail.stl

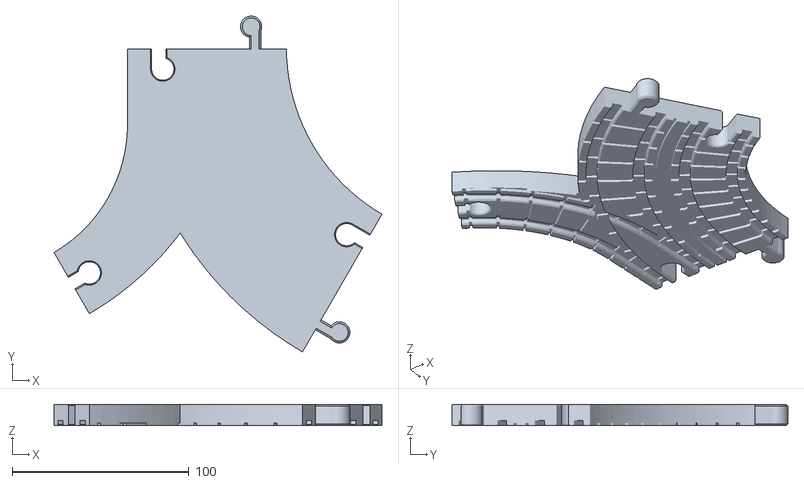
[picture p112: CAD file, 2017-08-04]
track60-stl/track60-switch11-rail.stl
185.6 x 190.1 x 12.0
