cscott/3d-track60/track60-stl/track60-switch8-road.stl

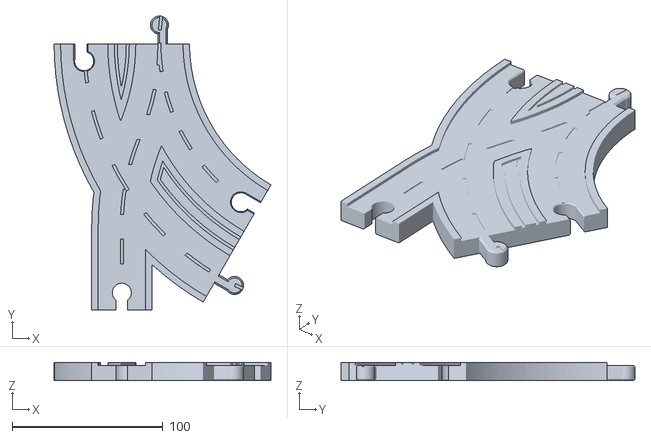
[picture p113: CAD file, 2017-08-04]
track60-stl/track60-switch8-road.stl
144.1 x 195.3 x 12.0
