cscott/3d-track60/track60.scad

/* Dave Barber's 60-degree brio track system */

// XXX switch6 says "may not be a valid 2-manifold"
// XXX -right/-left,-rail/-road will probably need to be
//     -left-road, -right-road, etc for pieces w/ double connectors.

// Based on:
//   http://tamivox.org/dave/train/sect14/gallery.pdf
// Added: O - mirrored B
// Added: p - one half of a double-track curve
// Added: q - one half of a double-track straight
// Added: R - half straight
// Added: 0 - dbl crossover
// Added: 1-7: combinations of double-to-single paths
// Added: 8 - dbl ramp
// Added: 9 - dbl buffer
// Added: < - like 2, but with offset = 0
// Added: > - like 2, but with offset = 1
// Added: ! - like 1, but with just_curve=true
// Added: $ - like 4, but with just_curve=true
// Added: / - like T, but rotated +15 deg (for dbl_roundabout)
// Added: \ - like T, but rotated -15 deg (for dbl_roundabout)
// Added: )( - straight double for dbl_roundabout

// Added: + - rotate remainder of the string by 60 degrees
// Added: = - rotate remainder of the string by -60 degrees

// Translation between old and new names:
// curve: BS
// dbl_curve: bs
// straight: AT
// dbl_straight: at
// half_straight: AR
// half_dbl_straight: ar
// crossing1: CS
// crossing2: BV
// crossing3: AW
// crossing4: EV
// crossing5: AZ
// crossing6: 00
// crossing7: 24/12*
// crossing8: 42/21
// crossing9: 14
// crossing10:41
// switch1: BT/BU*
// switch2: DU
// switch3: EU/ET*
// switch4: DS
// switch5: HS
// switch6: 22
// switch7: bs2A/osA2*
// switch8: bsA2/os2A*
// switch9: auA4/au1A*
// switch10:auA1/au4A*
// switch11:bs1A/osA4*
// switch12:bsA1/os4A*
// switch13:au0A/auA0*
// switch14:44/11*
// switch15:54/15*
// switch16:45/51*
// switch17: CT
// misc1: JS
// misc2: GS
// misc3: EW
// misc4: KS
// dbl_buffer: 88
// dbl_ramp: 99
// grade-crossing3: AW-1

/* [Global] */
part = "straight"; // [curve:Basic 60 degree curve,straight:Straight,half_straight:Special half-length straight,half_dbl_straight:Special half-length double straight,crossing1:Crossing #1 (two curves),crossing2:Crossing #2 (one curve one straight),crossing3:Crossing #3 (two straights),crossing4:Crossing #4 (two curves one straight),crossing5:Crossing #5 (three straights),crossing6:Crossing #6 (double xover),crossing7-left:Crossing #7 (double to single; one left one straight),crossing7-right:Crossing #7 (double to single; one right one straight),crossing7-rail:Crossing #7 alternate (rails),crossing7-road:Crossing #7 alternate (road),crossing8-left:Crossing #8 (double to single xover; one left one straight),crossing8-right:Crossing #8 (double to single xover; one right one straight),crossing8-rail:Crossing #8 alternate (rails),crossing8-road:Crossing #8 alternate (road),crossing9:Crossing #9 (double to single; one left one right),crossing10:Crossing #10 (double to single xover; one left one right),switch1-left:Switch #1 (left hand),switch1-right:Switch #1 (right hand),switch1-rail:Switch #1 alternate (rails),switch1-road:Switch #1 alternate (road),switch2:Switch #2,switch3-left:Switch #3 (left hand),switch3-right:Switch #3 (right hand),switch3-rail:Switch #3 alternate (rails),switch3-road:Switch #3 alternate (road),switch4:Switch #4,switch5:Switch #5,switch6:Switch #6 (single to double),switch7-left:Switch #7 (left hand curved double to straight single wye),switch7-right:Switch #7 (right hand curved double to straight single wye),switch7-rail:Switch #7 alternate (rails),switch7-road:Switch #7 alternate (road),switch8-left:Switch #8 (left hand curved double to xover straight single wye),switch8-right:Switch #8 (right hand curved double to xover straight single wye),switch8-rail:Switch #8 alternate (rails),switch8-road:Switch #8 alternate (road),switch9-left:Switch #9 (straight double to left curved single wye),switch9-right:Switch #9 (straight double to right curved single wye),switch9-rail:Switch #9 alternate (rails),switch9-road:Switch #9 alternate (road),switch10-left:Switch #10 (straight double to xover left curved single wye),switch10-right:Switch #10 (straight double to xover right curved single wye),switch10-rail:Switch #10 alternate (rails),switch10-road:Switch #10 alternate (road),switch11-left:Switch #11 (left hand curved double to right hand curved single wye),switch11-right:Switch #11 (right hand curved double to left hand curved single wye),switch11-rail:Switch #11 alternate (rails),switch11-road:Switch #11 alternate (road),switch12-left:Switch #12 (left hand curved double to xover right hand curved single wye),switch12-right:Switch #12 (right hand curved double to xover left hand curved single wye),switch12-rail:Switch #12 alternate (rails),switch12-road:Switch #12 alternate (road),switch13-left:Switch #13 (double straight left xover),switch13-right:Switch #13 (double straight right xover),switch13-rail:Switch #13 alternate (rails),switch13-road:Switch #13 alternate (road),switch14-left:Switch #14 (left hand curved double to single),switch14-right:Switch #14 (right hand curved double to single),switch14-rail:Switch #14 alternate (rails),switch14-road:Switch #14 alternate (road),switch15-left:Switch #15 (single-to-double left curved switch with right single curve),switch15-right:Switch #15 (single-to-double right curved switch with left single curve),switch15-rail:Switch #15 alternate (rails),switch15-road:Switch #15 alternate (road),switch16-left:Switch #16 (single-to-double left curved switch with right xover single curve),switch16-right:Switch #16 (single-to-double right curved switch with left xover single curve),switch16-rail:Switch #16 alternate (rails),switch16-road:Switch #16 alternate (road),switch17:Switch #17 (crossing #1 with added straight),misc1:Mixed switch and crossing #1,misc2:Mixed switch and crossing #2,misc3:Mixed switch and crossing #3,misc4:Mixed switch and crossing #4,roundabout-rail:Roundabout (assembled; w/ rails),roundabout-inner-straight-rail:Roundabout (inner piece; straight; w/ rails),roundabout-inner-crossing4-rail:Roundabout (inner piece; three way crossing; w/ rails),roundabout-outer-rail:Roundabout (outer piece; w/ rails),roundabout-road:Roundabout (assembled; w/ road),roundabout-inner-straight-road:Roundabout (inner piece; straight; w/ road),roundabout-inner-crossing4-road:Roundabout (inner piece; three way crossing; w/ road),roundabout-outer-road:Roundabout (outer piece; w/ road),dbl_roundabout-rail:Double-track roundabout (assembled; w/ rails),dbl_roundabout-inner-straight-rail:Double-track roundabout (inner piece; straight; w/ rails),dbl_roundabout-inner-dbl_straight-rail:Double-track roundabout (inner piece; double-track straight; w/ rails),dbl_roundabout-inner-crossing-rail:Double-track roundabout (inner piece; single and double-track crossing; w/ rails),dbl_roundabout-outer-rail:Double-track roundabout (outer piece; w/ rail),dogbone:Male-male connector,dbl_straight:Double-track straight,dbl_curve:Double-track curve,slope:Straight slope,slope-rail:Straight slope (rail only),slope-road:Straight slope (road only),curved-slope:Curved slope,big-slope:Double-length straight slope,big-curved-slope:Double-length curved slope,curved-slope-with-base-rail,curved-slope-with-base-road,riser:Riser (print on its side),buffer-rail:Buffer for rail,buffer-road:Buffer for road,ramp-rail:Ramp for rail,ramp-road:Ramp for road,dbl_buffer-rail:Double-track buffer for rail,dbl_buffer-road:Double-track buffer for road,dbl_ramp-rail:Double-track ramp for rail,dbl_ramp-road:Double-track ramp for road,barn:John Deere Barn connector,barn-dogbone:Special dogbone to connect John Deere Barn connector track,pez:Pez factory/First Response station adapter,pez2:Pez factory/First Response station adapter (alternate),carwash:Texaco Carwash connector,firehouse:Thomas' Firehouse connector,recycling-left:Recycling center adapter (left side),recycling-right:Recycling center adapter (right side),recycling-split-left:Recycling center adapter (left side/one road one rail),recycling-split-right:Recycling center adapter (right side/one road one rail),thomas-crossing:Adapter for Thomas' grade crossing,gas-station-left,gas-station-right,post-office-road-blank,post-office-top-road-blank,post-office-bottom-road-blank,mcdonalds-top-road-blank,mcdonalds-bottom-road-blank,grade-crossing:Grade crossing (straight),name-CS-1-rail:Grade crossing (crossing #1),name-BV-1:Grade crossing (crossing #2),name-AW-1-rail:Grade crossing (crossing #3),name-EV-1:Grade crossing (crossing #4),name-atAV-1:Grade crossing (single over double),name-AV11:Single-to-double left switch #1,name-AT44:Single-to-double right switch #1,name-JS-6-road-blank:Double-V crossing (misc-1),name-bt:Double-track switch (switch #1 right),name-bu:Double-track switch (switch #1 left),name-BS==14:Double-track delta switch #1,name-pA+bs+pA:Double-track delta switch #2,name-pA++pA++pA:Double-track delta switch #3]

/* [Hidden] */
use <common/pie.scad>;
use <trains/tracklib.scad>;
use <trains/track-wooden/dog-bone.scad>;
use <trains/track-wooden/track-standard.scad>;
use <roundabout.scad>
use <common/strutil.scad>
use <common/extrude.scad>
use <common/arch.scad>

// Dave suggests a base radius of 200mm.
// The core hexagon will then have a diameter of
// (4/3)r, or 266.7mm, and a "flat side height"
// of 2r/sqrt(3), or 230.9mm.
//basic_radius = 200;
// We want to fit the core hexagon in a build
// area of 200mm square, so we suggested the following
// basic radius:
//basic_radius = 170;
// However, our wTrak-like system works nicely
// if 7 hex cells (flat-to-flat) are 49 inches, hence:
basic_radius = 154;
// For comparison, according to
// http://www.woodenrailway.info/track/trackguide.html
// the standard brio "E" curve has a centerline radius of 202mm
// and the tighter brio "E1" curve has a centerline radius of 110mm
// and the typical straights are 4.5in, 5.5in, and 8.5in (compared to our 7in)
function track60_basic_radius() = basic_radius;

// 64mm is brio standard; some other sets have 62mm risers.
// Split the difference, so we're more or less compatible with either.
function riser_height() = 63;

function straight_length(radius) = 2*radius/sqrt(3);

/* Option 1: */
function tie_spacing(basic_radius=basic_radius) =
  basic_radius*((1/sqrt(3))-(PI/6))*2/*to taste*/;
function tie_angle(arc_radius, basic_radius=basic_radius) =
  180 * tie_spacing(basic_radius) / (PI * arc_radius);
/* */

/* Option 2:
function tie_angle(arc_radius, basic_radius=basic_radius) = 6;
function tie_spacing(basic_radius=basic_radius) =
  (tie_angle(basic_radius, basic_radius) * PI * basic_radius) / 180;
/* */

function tie_height()=(wood_height()-wood_well_height())/2;
function tie_width()=2;
function well_tie_height()=1;

// In tracklib:
//  wood_well_spacing should be 19.15
//  wood_well_width() = (31.3 - wood_well_spacing())/2 = 6.075 ~= 6.1

function road_height() = (wood_height()-2);
function road_width() = wood_well_spacing() + 2*wood_well_width();

function stripe_width() = 2;
function stripe_height() = 1;

// gutter between double-track pieces.
function double_gutter() = 10;

// dbl_roundabout ring
function dbl_roundabout_ring() = 37;

function other_dir(dir) = (dir=="left")?"right":"left";
function other_surface(surface) =
  (surface == "road" ? "rail" : (surface == "rail" ? "road" : surface));

function flip_surface(surface) =
  let (s=split(surface, "-"))
    str(other_surface(s[0]), "-", other_surface(s[1]));

function surface_offsets(surface="road-rail") =
  let(off = wood_height() - road_height())
  [/*top*/ startswith(surface, "road-") ? off : 0,
   /*bottom*/ endswith(surface, "-road") ? off : 0 ];
// Since double-track connector is not mirror-symmetric, pieces which
// include a double track connector should be blanked on the side
// where the double-connector would be "wrong".  That is, rail has to
// be on the bottom and road on the top in order for the connector
// to mate properly.
function blank_dbl_surface(surface) =
  startswith(surface, "rail-") ?
    blank_dbl_surface(str("blank-", split(surface, "-")[1])) :
  endswith(surface, "-road") ?
    str(split(surface, "-")[0], "-blank") :
  surface;

// Make curves look nice.
$fn = 120;

track60_demo(part);

function is_surface(s) = (s=="road") || (s=="rail") || (s=="blank");
function track60_parse_suffix(part) =
  let(n=len(part), pos=rindexof(part, "-"))
  pos < 0 ? part :
  let (suffix=substr(part, pos+1, n-pos-1))
  is_surface(suffix) ?
  let(pos2=rindexof(part, "-", pos))
  (pos2 >= 0 && is_surface(substr(part, pos2+1, pos-pos2-1)) ?
   substr(part, 0, pos2) : substr(part, 0, pos)) :
  (suffix=="left"||suffix=="right"||suffix=="mirror") ?
  track60_parse_suffix(substr(part, 0, pos)) :
  part;

function strip_prefix(s, prefix) =
  strip_prefixes(s, [prefix]);

function strip_prefixes(s, prefixes, i=0) =
  let(l=len(prefixes))
  i >= l ? s:
  startswith(s, prefixes[i]) ?
  substr(s, len(prefixes[i])) :
  strip_prefixes(s, prefixes, i+1);

function strip_dbl(s) =
  strip_prefixes(s, ["dbl_right_", "dbl_left_", "dbl_"]);

// Sample instantiations
module track60_demo(part="curve_rail",r=basic_radius) {
  hex_edge = 2*r/3;

  base = track60_parse_suffix(part);
  suffix = substr(part, len(base), len(part)-len(base));

  dir=(endswith(suffix, "-right") || endswith(suffix, "-mirror")) ?
    "right" : "left";
  surface = let (s=split(substr(suffix,1),"-")) // "<top>-<bottom>"
    len(s) >= 2 && is_surface(s[0]) && is_surface(s[1]) ?
    str(s[0], "-", s[1]) :
    s[0] == "rail" ? "rail-rail" :
    s[0] == "road" ? "road-road" :
    s[0] == "blank" ? "blank-blank" :
    "road-rail";

  if (base=="curve") {
    curve60(r, dir, surface=surface);
  } else if (startswith(base, "name-")) {
    shortname60(r, substr(base, 5, len(base)-5), surface=surface);
  } else if (base=="straight") {
    straight60(r, surface=surface);
  } else if (base=="half_straight") {
    half_straight60(r, surface=surface);
  } else if (substr(base, 0, 8)=="crossing") {
    which = numat(base, 8, intonly=true);
    crossing60(r, which=which, dir=dir, surface=surface);
  } else if (substr(base, 0, 6)=="switch") {
    which = numat(base, 6, intonly=true);
    switch60(r, which=which, dir=dir, surface=surface);
  } else if (substr(base, 0, 4)=="misc") {
    which = numat(base, 4, intonly=true);
    misc60(r, which=which, surface=surface);
  } else if (strip_dbl(base)=="buffer" || strip_dbl(base)=="ramp") {
    buffer_or_ramp60(r, surface=surface, which=base);
  } else if (base=="roundabout") {
    track60_demo(part=str("roundabout-inner-straight",suffix),r=r);
    track60_demo(part=str("roundabout-outer",suffix),r=r);
  } else if (startswith(base, "roundabout-")) {
    // roundabout-inner-straight, roundabout-inner-crossing4, roundabout-outer
    roundabout60(r, part=substr(base, len("roundabout-")), surface=surface);
  } else if (base=="dbl_roundabout") {
    track60_demo(part=str("dbl_roundabout-inner-crossing",suffix),r=r);
    track60_demo(part=str("dbl_roundabout-outer",suffix),r=r);
  } else if (startswith(base, "dbl_roundabout-")) {
    dbl_roundabout60(r, part=strip_prefix(base, "dbl_roundabout-"), surface=surface);
  } else if (part=="dogbone") {
    // scale to account for roadway depth
    scale([1,1,road_height()/wood_height()]) dogbone(true);
  } else if (base=="dbl_straight") {
    dbl_straight60(r, surface=blank_dbl_surface(surface));
  } else if (base=="dbl_curve") {
    dbl_curve60(r, dir=dir, surface=blank_dbl_surface(surface));
  } else if (base=="half_dbl_straight") {
    half_dbl_straight60(r, surface=blank_dbl_surface(surface));
  } else if (base=="barn-assembled") {
    track60_demo(part=str("barn",suffix),r=r);
    track60_demo(part=str("barn-dogbone",suffix),r=r);
  } else if (base=="barn") {
    barn60(r, surface=surface);
  } else if (base=="barn-dogbone") {
    barn60(r, surface=surface, part="dogbone");
  } else if (base=="pez") {
    pez60(r, surface=surface);
  } else if (base=="pez2") {
    peztwo60(r, surface=surface);
  } else if (base=="carwash") {
    carwash60(r, surface=surface);
  } else if (base=="firehouse") {
    firehouse60(r, surface=blank_dbl_surface(surface));
  } else if (base=="recycling") {
    recycling60(r, dir=dir, surface=surface, split_surface=false);
  } else if (base=="recycling-split") {
    recycling60(r, dir=dir, surface=surface, split_surface=true);
  } else if (base=="gas-station") {
    difference() {
      gas_station60(r, dir=dir, surface=surface);
      for (i=[0,180])
        translate([0,0,wood_height()/2]) rotate([0,i,0])
        translate([0,0,-wood_height()/2])
          gas_station60(r, part="gas-station-cutout");
    }
    *gas_station60(r, surface=surface, part="gas-station");
  } else if (base=="post-office" ||
             base=="post-office-top" || base == "post-office-bottom") {
    which = (base=="post-office") ? "both" : split(base, "-")[2];
    post_office60(r, surface=surface, part="all", which=which);
    *post_office60(r, surface=surface, part="post-office");
    *post_office60(r, surface=surface, part="post-office-hexes");
  } else if (base=="mcdonalds" ||
             base=="mcdonalds-top" || base == "mcdonalds-bottom") {
    which = (base=="mcdonalds") ? "both" : split(base, "-")[1];
    mcdonalds60(r, surface=surface, part="all", which=which);
    *mcdonalds60(r, surface=surface, part="mcdonalds");
    *mcdonalds60(r, surface=surface, part="mcdonalds-hexes");
  } else if (base=="grade-crossing") {
    grade_crossing60(r);
  } else if (base=="thomas-crossing") {
    thomas_crossing60(r, surface="rail-blank");
  } else if (base=="slope") {
    slope60(r, surface=surface);
  } else if (base=="big-slope") {
    slope60(2*r, surface=surface);
  } else if (base=="curved-slope") {
    slope_curve60(r, surface=surface, dir=dir);
  } else if (base=="curved-slope-with-base") {
    nsurface = str(split(surface, "-")[0], "-blank");
    slope_curve60(r, surface=nsurface, dir=dir, part="base");
  } else if (base=="big-curved-slope") {
    slope_curve60(r, angle=120, dir=dir, surface=surface);
  } else if (base=="riser") {
    riser60();
  } else if (base=="dbl_dogbone") {
    dbl_dogbone(surface=surface);
  } else if (base=="dbl_dogbone_plug") {
    dbl_dogbone_plug(surface=surface);
  } else if (base=="test-track") {
    neck=23; // 1/2 dogbone length, plus a bit
    intersection() {
      translate([-wood_width(), -straight_length(r), -1])
        cube([2*wood_width(), straight_length(r)/2 + neck, wood_height() + 2]);
      straight60(r, surface=surface);
    }
  }
}

// Based on http://tamivox.org/dave/train/sect14/gallery.pdf
function num_tracks_for_letter(s) =
  (toupper(s) != s[0]) ? num_tracks_for_letter(toupper(s)[0]) :
  (s == "A" || s == "S" || s == "+" || s == "=") ? 0 :
  (s == "B" || s == "O" || s == "R" || s == "T" || s == "U" || s == "V" ||
   s == "0" || s == "1" || s == "2" || s == "4" || s == "8" || s == "9" ||
   s == "<" || s == ">" || s == "!" || s == "$" || s == "P" || s == "Q" ||
   s == "/" || s == "\\"|| s == "(" || s == ")" ) ? 1 :
  (s == "C" || s == "D" || s == "E" || s == "W" || s == "X" || s == "Y" ||
   s == "3" || s == "5" || s == "6" ) ? 2 :
  (s == "J" || s == "K" || s == "L") ? 4 :
  s == "M" ? 5 :
  s == "N" ? 6 : 3;

function num_tracks_for_shortname(s) = let (n=len(s)) n == 0 ? 0 :
  let (dash=indexof(s, "-"))
  dash >= 0 ? num_tracks_for_shortname(substr(s, 0, dash)) :
  num_tracks_for_letter(s[0]) + num_tracks_for_shortname(substr(s, 1, n-1));

function name_has_dbl(s) = let (n=len(s)) n == 0 ? false :
  let (dash=indexof(s, "-"))
  dash >= 0 ? name_has_dbl(substr(s, 0, dash)) :
  (let (c=s[0]) toupper(c) != c ? true :
  (c == "0" || c == "1" || c == "2" || c == "3" || c == "4" ||
   c == "5" || c == "6" || c == "7" || c == "8" || c == "9" ||
   c == "<" || c == ">" || s == "!" || s == "$" ||
   c == "(" || c == ")") ? true :
  name_has_dbl(substr(s, 1, n-1)));

module maybe_dbl_curve60(radius, dir, surface, part, is_double) {
  if (is_double) {
    dbl_curve60(radius, dir, surface=surface, part=part);
  } else {
    curve60(radius, dir, surface=surface, part=part);
  }
}

module maybe_dbl_straight60(radius, surface, part, is_double) {
  if (is_double) {
    dbl_straight60(radius, surface=surface, part=part);
  } else {
    straight60(radius, surface=surface, part=part);
  }
}

function bitwise_and_nonzero(a, b) =
  (a == 0 || b == 0) ? false :
  let (lsb_a = (a % 2), lsb_b = (b % 2))
  (lsb_a != 0 && lsb_b != 0) ? true :
  bitwise_and_nonzero((a-lsb_a)/2, (b-lsb_b)/2);

module decode_shortname(s, i, radius, surface, part, flip_mask=0, is_even=false) {
  off = len(s) - 1;
  n = (len(s) <= 0 || s[off] == "-") ? 0 :
    num_tracks_for_letter(s[off]);
  c = toupper(s[off]);
  is_double = (s[off] != c); // lowercase means double track
  dash_pos = indexof(s, "-");
  if (s == "") {
    /* nothing */
    if (part != "body") bogus60(radius);
  } else if (dash_pos >= 0) {
    nmask = numat(s, dash_pos+1, intonly=true);
    decode_shortname(substr(s, 0, dash_pos), i, radius, surface, part,
                     flip_mask=nmask, is_even=is_even);
  } else if (c == "+" || c == "=") {
    rotate([0,0, c=="+" ? 60 : -60])
      decode_shortname(substr(s, 0, len(s)-1), i, radius, surface, part,
                       flip_mask=flip_mask, is_even=is_even);
  } else if (i >= n) {
    decode_shortname(substr(s, 0, len(s)-1), i-n, radius, surface, part,
                     flip_mask=floor(flip_mask/pow(2, n)), is_even=!is_even);
  } else if (flip_mask != 0) {
    nsurface = bitwise_and_nonzero(pow(2, i), flip_mask) ?
      flip_surface(surface) : surface;
    decode_shortname(s, i, radius, nsurface, part,
                     flip_mask=0, is_even=is_even);
  } else if (part == "body-well-road" || part == "body-well-rail") {
    which = split(part, "-")[2];
    surf = split(surface, "-");
    intersection() {
      with_bogus60(radius)
        decode_shortname(s, i, radius, surface, "body-well",
                         flip_mask=flip_mask, is_even=is_even);
      with_bogus60(radius) {
        if (surf[0] == which) {
          translate([0,0,wood_height()])
            cube([2*radius, 2*radius, wood_height()], center=true);
        }
        if (surf[1] == which) {
          cube([2*radius, 2*radius, wood_height()], center=true);
        }
      }
    }
  } else if (
    (c == "B" && i == 0) ||
    (c == "C" && i == 0) ||
    (c == "D" && i == 0) ||
    (c == "E" && i == 0) ||
    (c == "F" && i == 0) ||
    (c == "G" && i == 0) ||
    (c == "H" && i == 0) ||
    (c == "N" && i == 0) ||
    (c == "O" && i == 0)) {
    dir = (c == "O") ? "right" : "left";
    rotate([0,0,180])
      maybe_dbl_curve60(radius, dir, surface, part, is_double);
  } else if (
    (c == "I" && i == 0) ||
    (c == "J" && i == 0) ||
    (c == "K" && i == 0) ||
    (c == "L" && i == 0) ||
    (c == "M" && i == 0) ||
    (c == "N" && i == 1)) {
    rotate([0,0,120])
      maybe_dbl_curve60(radius, "left", surface, part, is_double);
  } else if (
    (c == "H" && i == 1) ||
    (c == "I" && i == 1) ||
    (c == "J" && i == 1) ||
    (c == "K" && i == 1) ||
    (c == "L" && i == 1) ||
    (c == "M" && i == 1) ||
    (c == "N" && i == 2)) {
    rotate([0,0,60])
      maybe_dbl_curve60(radius, "left", surface, part, is_double);
  } else if (
    (c == "E" && i == 1) ||
    (c == "F" && i == 1) ||
    (c == "K" && i == 2) ||
    (c == "L" && i == 2) ||
    (c == "M" && i == 2) ||
    (c == "N" && i == 3)) {
    rotate([0,0,0])
      maybe_dbl_curve60(radius, "left", surface, part, is_double);
  } else if (
    (c == "D" && i == 1) ||
    (c == "G" && i == 1) ||
    (c == "H" && i == 2) ||
    (c == "I" && i == 2) ||
    (c == "J" && i == 2) ||
    (c == "L" && i == 3) ||
    (c == "M" && i == 3) ||
    (c == "N" && i == 4)) {
    rotate([0,0,-60])
      maybe_dbl_curve60(radius, "left", surface, part, is_double);
  } else if (
    (c == "C" && i == 1) ||
    (c == "F" && i == 2) ||
    (c == "G" && i == 2) ||
    (c == "J" && i == 3) ||
    (c == "K" && i == 3) ||
    (c == "M" && i == 4) ||
    (c == "N" && i == 5)) {
    rotate([0,0,-120])
      maybe_dbl_curve60(radius, "left", surface, part, is_double);
  } else if (
    (c == "T" && i == 0) ||
    (c == "W" && i == 1) ||
    (c == "X" && i == 1) ||
    (c == "Z" && i == 2)) {
    rotate([0,0,60])
      maybe_dbl_straight60(radius, surface, part, is_double);
  } else if (
    (c == "U" && i == 0) ||
    (c == "W" && i == 0) ||
    (c == "Y" && i == 0) ||
    (c == "Z" && i == 0)) {
    maybe_dbl_straight60(radius, surface, part, is_double);
  } else if (
    (c == "V" && i == 0) ||
    (c == "X" && i == 0) ||
    (c == "Y" && i == 1) ||
    (c == "Z" && i == 1)) {
    rotate([0,0,-60])
      maybe_dbl_straight60(radius, surface, part, is_double);
  } else if (
    (c == "1" && i == 0) ||
    (c == "3" && i == 0) ||
    (c == "5" && i == 0) ||
    (c == "7" && i == 0) ||
    (c == "!" && i == 0)) {
    rotate([0,0,180])
    dbl_curve_sway60(radius, dir="right", surface=surface, part=part,
                     far_side=!is_even, just_curve=(c=="!"));
  } else if (
    (c == "2" && i == 0) ||
    (c == "3" && i == 1) ||
    (c == "6" && i == 0) ||
    (c == "7" && i == 1) ||
    (c == "<" && i == 0) ||
    (c == ">" && i == 0)) {
    dbl_sway60(radius, is_even ? "left" : "right", surface=surface, part=part,
               offset=(c=="<") ? 0 : (c==">") ? 1 : 0.5);
  } else if (
    (c == "4" && i == 0) ||
    (c == "5" && i == 1) ||
    (c == "6" && i == 1) ||
    (c == "7" && i == 2) ||
    (c == "$" && i == 0)) {
    rotate([0,0,180])
    dbl_curve_sway60(radius, dir="left", surface=surface, part=part,
                     far_side=is_even, just_curve=(c=="$"));
  } else if ((c == "0" && i == 0)) {
    dbl_sway60(radius, is_even ? "left" : "right", surface=surface, part=part,
               sway_far=true);
  } else if (
    (c == "8" && i == 0) ||
    (c == "9" && i == 0)) {
    which = str("dbl_",
                is_even ? "left_" : "right_",
                c == "8" ? "buffer" : "ramp");
    rotate([0,0,180])
      buffer_or_ramp60(radius, surface=surface, part=part, which=which);
  } else if ((c == "R" && i == 0)) {
    half_straight60(radius, surface=surface, part=part, double=is_double);
  } else if (
    (c == "/" && i == 0) ||
    (c == "\\" && i == 0)) {
    rotate([0,0,60 + (c == "/" ? 15 : -15)])
      straight60(radius, surface, part);
  } else if (
    (c == "(" && i == 0) ||
    (c == ")" && i == 0)) {
    scale([(c=="(")?-1:1,1,1])
      dbl_roundabout60_inner_curve(radius, surface=surface, part=part);
  } else if ((c == "P" && is_double && i == 0)) {
    dbl_curve60(radius, dir="left", surface=surface, part=part,
                   only_left=is_even, only_right=!is_even);
  } else if ((c == "Q" && is_double && i == 0)) {
    dbl_straight60(radius, surface, part,
                   only_left=is_even, only_right=!is_even);
  }
}

module shortname60(radius=basic_radius, name="BS", surface="road-rail",
                   part="all", is_intersection=false) {
  if (part=="all") {
    has_double = name_has_dbl(name);
    nsurface = has_double ? blank_dbl_surface(surface) : surface;
    difference() {
      union() {
        shortname60(radius, name, nsurface, "body");
        if (has_double) shortname60(radius, name, nsurface, "gutter");
      }
      difference() {
        shortname60(radius, name, nsurface, "hole");
        intersection() {
          with_bogus60(radius)
          shortname60(radius, name, nsurface, "body-well-road");
          with_bogus60(radius)
          shortname60(radius, name, nsurface, "body-well-rail");
        }
      }
      shortname60(radius, name, nsurface, "connector");
      shortname60(radius, name, nsurface, "ties-nonoverlapping");
    }
  } else if (part=="ties-nonoverlapping") {
    difference() {
      with_bogus60(radius)
        shortname60(radius, name, surface, "ties");
      shortname60(radius, name, surface, "body", is_intersection=true);
    }
  } else if (part=="gutter") {
    trim_gutter60(radius, surface) {
      shortname60(radius, name, surface, "gutter-body");
      shortname60(radius, name, surface, "body");
    }
  } else {
    num = num_tracks_for_shortname(name);
    union_or_intersection(is_intersection=is_intersection, nchildren=num) {
      decode_shortname(name, 0, radius, surface, part);
      decode_shortname(name, 1, radius, surface, part);
      decode_shortname(name, 2, radius, surface, part);
      decode_shortname(name, 3, radius, surface, part);
      decode_shortname(name, 4, radius, surface, part);
      decode_shortname(name, 5, radius, surface, part);
      decode_shortname(name, 6, radius, surface, part);
      decode_shortname(name, 7, radius, surface, part);
      decode_shortname(name, 8, radius, surface, part);
      decode_shortname(name, 9, radius, surface, part);
      decode_shortname(name, 10, radius, surface, part);
      decode_shortname(name, 11, radius, surface, part);
      decode_shortname(name, 12, radius, surface, part);
      decode_shortname(name, 13, radius, surface, part);
      decode_shortname(name, 14, radius, surface, part);
      decode_shortname(name, 15, radius, surface, part);
      decode_shortname(name, 16, radius, surface, part);
      decode_shortname(name, 17, radius, surface, part);
    }
  }
}

module trim_gutter60(radius, surface) {
  off = (wood_height() - wood_well_height())/2;
  offset_top = startswith(surface, "blank-") ? 0 : off;
  offset_bottom = endswith(surface, "-blank") ? 0 : off;
  height = wood_height() - offset_top - offset_bottom;

  intersection() {
    children(0); // part="gutter-body"
    translate([-2*radius, -2*radius, offset_bottom])
      cube([4*radius, 4*radius, height]);
  }
  if (height < wood_height()) difference() {
    children(0); // part="gutter-body"
    minkowski() {
      cylinder(r=2, h=2*wood_height(), center=true, $fn=6);
      children(1); // part="body"
    }
  }
}

module union_or_intersection(is_intersection=false, nchildren=undef) {
  num = (nchildren!=undef) ? nchildren : $children;
  if (is_intersection) {
    for(i=[0:1:num-2]) {
      for(j=[i+1:1:num-1]) {
        intersection() { children(i); children(j); }
      }
    }
  } else {
    union() children();
  }
}

module bogus60(radius) {
  // something guaranteed to have an empty intersection with the core hex
  translate([10*radius,10*radius,10*wood_height()]) cube([.1,.1,.1]);
}

module with_bogus60(radius, disable=false) {
  children();
  if (!disable) bogus60(radius);
}

// Most crossings are mirror symmetric, but the `dir` parameter is used for
// those which aren't.
module crossing60(radius, which, dir="left", surface="road-rail", part="all") {
  if (which==1) {
    shortname60(radius=radius, name="CS", surface=surface, part=part);
  } else if (which==2) {
    shortname60(radius=radius, name="BV", surface=surface, part=part);
  } else if (which==3) {
    shortname60(radius=radius, name="AW", surface=surface, part=part);
  } else if (which==4) {
    shortname60(radius=radius, name="EV", surface=surface, part=part);
  } else if (which==5) {
    shortname60(radius=radius, name="AZ", surface=surface, part=part);
  } else if (which==6) {
    // double crossover
    shortname60(radius=radius, name="00", surface=surface, part=part);
  } else if (which==7) {
    // double-to-single crossover (crossing #7 is technically a gantlet)
    // one straight, one curved.
    shortname60(radius=radius, name=(dir=="left"?"24":"12"), surface=surface, part=part);
  } else if (which==8) {
    // double-to-single crossover (crossing #7 is technically a gantlet)
    // one straight, one curved.
    shortname60(radius=radius, name=(dir=="left"?"42":"21"), surface=surface, part=part);
  } else if (which==9) {
    // double-to-single crossover (crossing #9 is technically a gantlet)
    // both curved
    shortname60(radius=radius, name="14", surface=surface, part=part);
  } else if (which==10) {
    // double-to-single crossover (crossing #9 is technically a gantlet)
    // both curved
    shortname60(radius=radius, name="41", surface=surface, part=part);
  }
}

// Some switches are mirror symmetric, but the `dir` parameter is used for
// those which aren't.
module switch60(radius, which, dir="left", surface="road-rail", part="all",
                is_intersection=false) {
  if (which==1) {
    shortname60(radius=radius, name=(dir=="left"?"BU":"BT"), surface=surface, part=part);
  } else if (which==2) {
    shortname60(radius=radius, name="DU", surface=surface, part=part);
  } else if (which==3) {
    shortname60(radius=radius, name=(dir=="left"?"EU":"ET"), surface=surface, part=part);
  } else if (which==4) {
    shortname60(radius=radius, name="DS", surface=surface, part=part);
  } else if (which==5) {
    shortname60(radius=radius, name="HS", surface=surface, part=part);
  } else if (which==6) {
    // single-to-double straight switch
    shortname60(radius=radius, name="22", surface=surface, part=part);
  } else if (which==7) {
    // curved double-to-straight single wye
    // optimized offset -- but maybe default is actually better?
    shortname60(radius=radius, name=(dir=="left"?"bs>A":"osA>"), surface=surface, part=part);
  } else if (which==8) {
    // curved double-to-straight single wye
    // optimized offset -- but maybe default is actually better?
    shortname60(radius=radius, name=(dir=="left"?"bsA<":"os<A"), surface=surface, part=part);
  } else if (which==9) {
    // straight double-to-curved single wye
    shortname60(radius=radius, name=(dir=="left"?"auA$":"au!A"), surface=surface, part=part);
  } else if (which==10) {
    // straight double-to-curved single wye
    shortname60(radius=radius, name=(dir=="left"?"au$A":"auA!"), surface=surface, part=part);
  } else if (which==11) {
    // curved double to curved single wye
    shortname60(radius=radius, name=(dir=="left"?"bs1A":"osA4"), surface=surface, part=part);
  } else if (which==12) {
    // curved double to curved single wye
    shortname60(radius=radius, name=(dir=="left"?"bsA1":"os4A"), surface=surface, part=part);
  } else if (which==13) {
    // double-track crossover
    shortname60(radius=radius, name=(dir=="left"?"au0A":"auA0"), surface=surface, part=part);
  } else if (which==14) {
    // single-to-double curved switch
    shortname60(radius=radius, name=(dir=="left"?"44":"11"), surface=surface, part=part);
  } else if (which==15) {
    // single-to-double curved switch, with right single curve
    shortname60(radius=radius, name=(dir=="left"?"54":"15"), surface=surface, part=part);
  } else if (which==16) {
    // single-to-double curved switch, with right single curve
    shortname60(radius=radius, name=(dir=="left"?"45":"51"), surface=surface, part=part);
  } else if (which==17) {
    shortname60(radius=radius, name="CT", surface=surface, part=part);
  }
}

module misc60(radius, which, surface="road-rail", part="all", is_intersection=false) {
  if (which==1) {
    shortname60(radius=radius, name="JS", surface=surface, part=part);
  } else if (which==2) {
    shortname60(radius=radius, name="GS", surface=surface, part=part);
  } else if (which==3) {
    shortname60(radius=radius, name="EW", surface=surface, part=part);
  } else if (which==4) {
    shortname60(radius=radius, name="KS", surface=surface, part=part);
  }
}

module buffer_or_ramp60(radius, surface="road-rail", part="all",
                        which="buffer", trim_ties=true) {
  is_double = startswith(which, "dbl_");
  double_dir = (!is_double) ? [0] :
    concat(startswith(which, "dbl_right_") ? [] : [1],
           startswith(which, "dbl_left_") ? [] : [-1]);
  clearance = !is_double ? 1 :
    /* needs to clear double connector */ -8;
  half_width = wood_width()/2;
  inner_radius = radius - half_width;
  width_adj = inner_radius - sqrt(pow(inner_radius,2) - pow(half_width,2));
  buflen = straight_length(radius)/2 /* half straigth */
    - (straight_length(radius) - inner_radius) /* clear a curve60 */
    - width_adj /* shorten to account for non-zero width of buffer */
    - clearance /* a smidge more */;

  buffer_total_height = 33.5;
  buffer_stop_height = 10.5;
  buffer_stop_depth = 8;
  buffer_depth = buffer_total_height - wood_height() + 3.5;
  buffer_total_depth = buffer_depth + buffer_stop_depth;
  zigzag_width = 5;
  zigzag_depth = 0.6;
  num_zigzag = ceil(wood_width() / (2*zigzag_width));
  ramp_start = is_double ? 19 : 10;
  ramp_min_thick = 0.3; // height of first layer
  buffer = endswith(which, "buffer");
  ramp = endswith(which, "ramp");
  pivot_point = [0, -straight_length(radius)/2 + ramp_start, wood_height()];
  // road => road on top.  else rail on top.
  ramp_angle = atan2((startswith(surface, "road-") ?
                      road_height() : wood_well_height()) - ramp_min_thick,
                     buflen - ramp_start);
  // ensure surface ends in '-blank'
  nsurface = let (sp=split(surface, "-"))
    sp[0] == "blank" ? str(sp[1], "-", sp[0]) :
    str(sp[0], "-", "blank");
  mirror_connector = is_double && startswith(nsurface, "rail-");

  if (part=="all") {
    difference() {
      union() {
        buffer_or_ramp60(radius, nsurface, "body", which=which);
        buffer_or_ramp60(radius, nsurface, "gutter", which=which);
      }
      buffer_or_ramp60(radius, nsurface, "hole", which=which);
      buffer_or_ramp60(radius, nsurface, "connector", which=which);
      buffer_or_ramp60(radius, nsurface, "ties", which=which, trim_ties=false);
    }
  } else if (part=="ties" && trim_ties) {
    intersection() {
      with_bogus60(radius)
        buffer_or_ramp60(radius, surface=nsurface, part="ties", which=which, trim_ties=false);
      buffer_or_ramp60(radius, surface=nsurface, part="body", which=which);
    }
  } else if (part=="body" || part=="gutter" || part=="gutter-body") {
    newr = buflen*sqrt(3)/2;
    // short straight
    difference() {
      with_bogus60(radius)
      translate([0,-straight_length(radius)/2 + buflen/2, 0]) {
        if (is_double) {
          scale([mirror_connector?-1:1,1,1])
          dbl_straight60(newr, surface=nsurface, part=part);
        } else if (part=="body") {
          straight60(newr, surface=nsurface, part=part);
        }
      }
      if (is_double) {
        // trim the protruding double connector
        cube([2*radius, straight_length(radius)-2*buflen, 2*radius],
             center=true);
        // trim the "other side"
        if (len(double_dir) < 2) {
          for (i=double_dir)
            translate([-i*(wood_width()+double_gutter())/2, 0, 0])
              cube([wood_width(), 2*radius, 2*radius], center=true);
        }
      }
      if (ramp) {
        translate(pivot_point) rotate([-ramp_angle,0,0]) translate(-pivot_point)
        translate([0,0,radius + wood_height()])
          cube([2*radius, 2*radius, 2*radius], center=true);
      }
    }
    // male connector
    if (part=="body" && !is_double) translate([0,-straight_length(radius)/2, 0])
      scale([1,1,startswith(surface, "rail-")?1:(road_height()/wood_height())])
        rotate([0,0,-90]) wood_plug();
    // buffer
    if (part=="body" && buffer) {
      buffer_or_ramp60(radius, nsurface, part="buffer", which=which);
    }
  } else if (part=="buffer") {
    for (i=double_dir)
    translate([i*(wood_width()+double_gutter())/2, 0, 0])
    difference() {
      translate([-half_width,
               -straight_length(radius)/2 + buflen - buffer_depth,
               0]) {
        cube([wood_width(), buffer_depth, buffer_total_height]);
        translate([0, -buffer_stop_depth,
                   buffer_total_height - buffer_stop_height]) {
          cube([wood_width(), buffer_total_depth, buffer_stop_height]);
          // Fill in the underhang for support-free printing.
          rotate([-45,0,0])
          cube([wood_width(), buffer_stop_depth*sqrt(2)+1, buffer_stop_height]);
        }
      }
      translate([-half_width-1, -straight_length(radius)/2 + buflen,
                  wood_height()])
        rotate([45,0,0])
          cube([wood_width()+2, radius, 2*buffer_total_depth]);
      // zig zag pattern
      rotate([0,45,0])
      for (i=[-num_zigzag:1:num_zigzag])
        translate([i*2*zigzag_width,
                   -straight_length(radius)/2 + buflen - buffer_total_depth,
                   buffer_total_height - (buffer_stop_height/2)])
         cube([zigzag_width, 2*zigzag_depth, 2*buffer_total_height],
              center=true);
    }
  } else if (part=="connector") {
    if (is_double) {
      scale([mirror_connector?-1:1,1,1])
        dbl_straight60(radius, surface=nsurface, part=part,
                       trim_ties=trim_ties);
    } else {
      bogus60(radius); /* nothing! */
    }
  } else {
    // hole and ties are unscaled to preserve consistent spacing.
    // but make this single-sided (ie, use nsurface)
    difference() {
      with_bogus60(radius)
        if (is_double) {
          dbl_straight60(radius, surface=nsurface, part=part,
                         trim_ties=trim_ties);
        } else {
          straight60(radius, surface=nsurface, part=part,
                     trim_ties=trim_ties);
        }
      if (buffer) {
        buffer_or_ramp60(radius, nsurface, part="buffer", which=which);
      }
      // don't step on the front connector
      translate([0,-straight_length(radius)/2 - radius/2 - .01,0])
        cube([radius, radius, 3*wood_height()], center=true);
    }
    if (ramp && part != "connector") {
      difference() {
        with_bogus60(radius)
        translate(pivot_point) rotate([-ramp_angle,0,0]) translate(-pivot_point)
          if (is_double) {
            dbl_straight60(radius, surface=nsurface, part=part,
                           trim_ties=trim_ties);
          } else {
            straight60(radius, surface=nsurface, part=part,
                       trim_ties=trim_ties);
          }
        translate([0,0,-radius + ramp_min_thick])
          cube([2*radius, 2*radius, 2*radius], center=true);
      }
    }
  }
}

// centered on the hex center
module straight60(radius, surface="road-rail", part="all") {
  track_parts(radius, surface, part, gutter=false, mirror_symmetric=true) {
    // body
    translate([wood_width()/2,-straight_length(radius)/2,0])
      rotate([0,0,90]) wood_track(straight_length(radius), false);
    // gutter-body
    straight60(radius, surface, "gutter-body-nope");
    // rails
    translate([0,-straight_length(radius)/2,0])
      wood_rails_and_ties(radius, part="rails");
    // ties
    translate([0,-straight_length(radius)/2,0])
      wood_rails_and_ties(radius, part="ties");
    // roads
    translate([0,-straight_length(radius)/2,0])
      wood_road_and_stripes(radius);
    // connector
    for (i=[1,-1]) {
      translate([0,i*straight_length(radius)/2,0]) rotate([0,0,(i+1)*90])
        loose_wood_cutout();
    }
    // other
    if (part=="body-well") {
      translate([0,0,wood_height()/2])
        cube([wood_well_spacing(), straight_length(radius), wood_height()],
             center=true);
    }
  }
}

module half_dbl_straight60(radius, surface="road-rail", part="all") {
  half_straight60(radius, surface=surface, part=part, double=true);
}

module half_straight60(radius, surface="road-rail", part="all", trim_ties=true,
                       double=false, converter=false) {

  if (part=="all") {
    difference() {
      union() {
        half_straight60(radius, surface, "body", double=double);
        if (double) half_straight60(radius, surface, "gutter", double=double);
      }
      half_straight60(radius, surface, "hole", double=double);
      half_straight60(radius, surface, "connector", double=double);
      half_straight60(radius, surface, "ties", trim_ties=false, double=double);
    }
  } else if (part=="ties" && trim_ties) {
    intersection() {
      with_bogus60(radius)
        half_straight60(radius, surface=surface, part="ties",
                        trim_ties=false, double=double);
      half_straight60(radius, surface=surface, part="body", double=double);
    }
  } else if (part=="connector" && converter) {
    // hacky converter from two single tracks to double track.
    // used as an adapter for a long bridge piece I have, which is
    // otherwise a multiple of straight_length long and already has the
    // correct track spacing.
    for (i=[1,-1]) translate([i*(wood_width()+double_gutter())/2,0,0])
      straight60(radius, surface=surface, part=part);
    translate([0,-straight_length(radius),0])
      cube([radius, straight_length(radius), 3*wood_height()], center=true);
    rotate([0,0,180])
      dbl_connector(surface=surface, part=part);
  } else if (part=="body" || part=="connector" ||
             part=="gutter" || part=="gutter-body") {
    translate([0,-straight_length(radius)/4,0])
      if (double) {
        dbl_straight60(radius/2, surface=surface, part=part);
      } else {
        straight60(radius/2, surface=surface, part=part);
      }
  } else {
    // hole and ties are unscaled to preserve consistent spacing.
    if (double) {
      dbl_straight60(radius, surface=surface, part=part);
    } else {
      straight60(radius, surface=surface, part=part);
    }
  }
}

// centered on the hex center
module curve60(radius, dir, surface="road-rail", part="all") {
  norigin = [-radius,-straight_length(radius)/2,0];
  inner_radius = radius - (wood_width()/2);

  if (dir=="right") {
    scale([-1,1,1]) curve60(radius, "left", surface, part);
  } else translate(norigin) track_parts(radius, surface, part, gutter=false) {
    // body
    wood_track_arc(inner_radius, 60, false);
    // gutter-body
    curve60(radius, dir, surface, "gutter-body-nope");
    // rails
    wood_rails_and_ties_arc(radius, angle=60, part="rails", basic_radius=radius);
    // ties
    wood_rails_and_ties_arc(radius, angle=60, part="ties", basic_radius=radius);
    // roads
    wood_road_and_stripes_arc(radius, angle=60, basic_radius=radius);
    // connector
    union() {
      translate([radius,0,0])
        loose_wood_cutout();
      rotate([0,0,60]) translate([radius,0,0]) rotate([0,0,180])
        loose_wood_cutout();
    }
    // other
    if (part=="body-well") {
      ring(radius, 60, wood_height(), wood_well_spacing());
    }
  }
}

module wood_rails_and_ties(radius, part="both", length=undef, bevel_ends=true) {
  epsilon = .1;
  do_rails = (part=="both" || part=="rails");
  do_ties = (part=="both" || part=="ties");
  sl = length != undef ? length : straight_length(radius);

  if (do_rails) {
    translate([wood_width()/2,0,0])
      rotate([0,0,90]) wood_rails(sl, bevel_ends=bevel_ends);
  }

  spacing = tie_spacing(radius);
  num=ceil(sl/spacing);
  start = -ceil((straight_length(radius)/2)/spacing);

  // ties.
  intersection() {
    translate([-wood_width()/2-2*epsilon, -epsilon, 0])
      cube([wood_width()+4*epsilon, sl + 2*epsilon, wood_height() + epsilon]);
    for (i = [start:1:start+num] ) {
      translate([0,(straight_length(radius)/2)+(i-.5)*spacing,0]) {
        if (do_ties) {
          translate([-wood_width()/2-epsilon, -tie_width()/2, wood_height()-tie_height()])
            cube([wood_width()+2*epsilon, tie_width(), wood_height()]);
        }
        if (do_rails) for (j=[1,-1]) scale([j,1,1]) {
          translate([-(wood_well_spacing()/2)-wood_well_width(),
                     -tie_width()/2, wood_well_height() - well_tie_height()])
            cube([wood_well_width(), tie_width(), wood_height()]);
        }
      }
    }
  }
}

module wood_road_and_stripes(radius, length=undef) {
  sl = length != undef ? length : straight_length(radius);
  epsilon = 1;

  translate([-road_width()/2,-epsilon,road_height()])
    cube([road_width(), sl + 2*epsilon, wood_height()]);

  spacing = tie_spacing(radius)*2;
  num=ceil(sl/spacing);
  start = -ceil((straight_length(radius)/2)/spacing);

  // stripes.
  intersection() {
    translate([-road_width()/2,-epsilon, 0])
      cube([road_width(), sl + 2*epsilon, wood_height() + epsilon]);
    for (i = [start:1:start+num] ) {
      translate([0,(straight_length(radius)/2)+(i+.25)*spacing,0]) {
        translate([-stripe_width()/2,0,road_height()-stripe_height()])
          cube([stripe_width(),spacing/2, stripe_height() + epsilon]);
      }
    }
  }
}


module wood_road_and_stripes_arc(radius, angle,
                                 basic_radius=basic_radius,
                                 stripes_from_start=false,
                                 stripes_from_end=false) {
  epsilon = 1;
  translate([0,0,road_height()]) {
    difference() {
      pie(radius + road_width()/2, angle, wood_height());
      translate([0,0,-epsilon])
        pie(radius - road_width()/2, angle + 2*epsilon,
            wood_height() + 2*epsilon, -epsilon);
    }
  }
  angle_increment = tie_angle(arc_radius=radius, basic_radius=basic_radius)*2;
  num=ceil((angle/angle_increment)/2);

  // stripes.
  intersection() {
    pie(radius + wood_width()/2,
        angle + 2*epsilon,
        wood_height() + epsilon,
        -epsilon);
  for (i = (stripes_from_start||stripes_from_end)?[0.5:1:2*num]:[-num:1:num] ) {
    a =
      stripes_from_start ? (i-0.25)*angle_increment :
      stripes_from_end ? (angle - (i-0.25)*angle_increment) :
      ((angle/2) + ((i-0.25)*angle_increment));
    rotate([0,0,a]) difference() {
      translate([0,0,road_height()-stripe_height()])
        pie(radius + stripe_width()/2, angle_increment/2,
            stripe_height() + epsilon);
      translate([0,0,road_height()-stripe_height()-epsilon])
        pie(radius - stripe_width()/2, angle_increment/2 + 2*epsilon,
            stripe_height() + 3*epsilon, -epsilon);
    }
  }
  }
}

module wood_rails_and_ties_arc(radius, angle, part="both", bevel_ends=false,
                               basic_radius=basic_radius,
                               ties_from_start=false,
                               ties_from_end=false) {
  epsilon=.1;
  do_rails = (part=="both" || part=="rails");
  do_ties = (part=="both" || part=="ties");

  inner_radius = radius - (wood_width()/2);

  angle_increment = tie_angle(arc_radius=radius, basic_radius=basic_radius);

  num=ceil((angle/angle_increment)/2);

  if (do_rails) wood_rails_arc(inner_radius, angle, bevel_ends=bevel_ends);

  intersection() {
    pie(radius + wood_width()/2,
        angle + 2*epsilon,
        wood_height() + epsilon,
        -epsilon);
  for (i = (ties_from_start||ties_from_end)?[0.5:1:2*num]:[-num:1:num] ) {
    a =
      ties_from_start ? i*angle_increment :
      ties_from_end ? (angle - i*angle_increment) :
      ((angle/2) + (i*angle_increment));
    rotate([0,0,a]) {
      if (do_ties) {
      translate([radius - wood_width()/2 - epsilon, -tie_width()/2, wood_height()-tie_height()])
        cube([wood_width()+2*epsilon, tie_width(), wood_height()]);
      }
      if (do_rails) for (j=[1,-1]) {
        translate([radius+j*(wood_well_spacing()/2)-(j<0?wood_well_width():0),
                   -tie_width()/2, wood_well_height() - well_tie_height()])
          cube([wood_well_width(), tie_width(), wood_height()]);
      }
    }
  }
  }
}

// Double-track pieces.
// centered on the hex center
module dbl_straight60(radius, surface="road-rail", part="all",
                      only_left=false, only_right=false) {
  epsilon=.1;

  track_parts(radius, surface, part, mirror_symmetric=true) {
    dbl_straight60(radius, surface, "split-body",
                   only_left=only_left, only_right=only_right);
    // gutter-body
    translate([0,0,wood_height()/2]) {
      cube([double_gutter()+epsilon, straight_length(radius),
            wood_height()], center=true);
    }
    dbl_straight60(radius, surface, "split-hole-rails",
                   only_left=only_left, only_right=only_right);
    dbl_straight60(radius, surface, "split-hole-ties",
                   only_left=only_left, only_right=only_right);
    dbl_straight60(radius, surface, "split-hole-road",
                   only_left=only_left, only_right=only_right);
    // connector
    for (i=[0,180]) rotate([0,0,i])
      translate([0,-straight_length(radius)/2,0])
        dbl_connector(surface=surface, part="connector");
    // other
    if (startswith(part, "split-")) {
      base = substr(part, len("split-"));
      rots = only_right ? [0] : only_left ? [180] : [0,180];
      for (i=rots) rotate([0,0,i]) {
        translate([(wood_width()+double_gutter())/2, 0, 0])
          straight60(radius, surface=surface, part=base);
        translate([0,straight_length(radius)/2,0])
          rotate([0,0,180])
            dbl_connector(surface=surface, part=base);
      }
    }
  }
}

module dbl_curve60(radius, dir, surface="road-rail", part="all",
                   trim_ties=true, only_left=false, only_right=false) {
  epsilon=.1;

  if (dir=="right") {
    scale([-1,1,1])
      dbl_curve60(radius, "left", surface, part, trim_ties=trim_ties,
                  only_left=only_right, only_right=only_left);
  } else if (part=="all") {
    difference() {
      union() {
        dbl_curve60(radius, dir, surface, "body",
                    only_left=only_left, only_right=only_right);
        dbl_curve60(radius, dir, surface, "gutter");
      }
      dbl_curve60(radius, dir, surface, "hole",
                  only_left=only_left, only_right=only_right);
      dbl_curve60(radius, dir, surface, "connector");
      dbl_curve60(radius, dir, surface, "ties", trim_ties=false,
                  only_left=only_left, only_right=only_right);
    }
  } else if (part=="gutter-body") {
    translate([-radius, -straight_length(radius)/2, 0])
      ring(radius, 60, wood_height(), double_gutter() + epsilon);
  } else if (part=="gutter") {
    trim_gutter60(radius, surface) {
      dbl_curve60(radius, dir, surface, "gutter-body");
      dbl_curve60(radius, dir, surface, "body");
    }
  } else if (part=="connector") {
    translate([-radius,-straight_length(radius)/2,0])
      for(i=[0,1]) rotate([0,0,i*60])
        translate([radius,0,0]) rotate([0,0,i*180])
          dbl_connector(surface=surface, part=part);
  } else {
    translate([-radius,-straight_length(radius)/2,0]) {
      rots = only_right ? [1] : only_left ? [-1] : [1,-1];
      for (i=rots) {
        nr = radius + i*(wood_width()+double_gutter())/2;
        ns = 2*nr/sqrt(3);
        translate([nr,ns/2,0])
          curve60(nr, "left", surface=surface, part=part, trim_ties=trim_ties);
        rotate([0,0,(i+1)*30])
          translate([radius,0,0]) rotate([0,0,(i+1)*90])
            dbl_connector(surface=surface, part=part);
      }
    }
  }
}

module dbl_sway60(radius, dir, surface="road-rail", part="all",
                  sway_far=false, offset=0.5, trim_ties=true) {
  if (dir=="right") {
    dbl_sway60_right(radius, surface, part, sway_far, offset, trim_ties);
  } else if (dir=="left") {
    dbl_sway60_left(radius, surface, part, sway_far, offset, trim_ties);
  } else { echo("bad direction", dir); }
}

module dbl_sway60_right(radius, surface="road-rail", part="all",
                        sway_far=false, offset=0.5, trim_ties=true) {
  scale([-1,1,1])
    dbl_sway60_left(radius=radius, surface=surface, part=part,
                    sway_far=sway_far, offset=offset,
                    trim_ties=trim_ties, mirror_connector=true);
}

module dbl_sway60_left(radius, surface="road-rail", part="all",
                       sway_far=false, offset=0.5,
                       trim_ties=true, mirror_connector=false) {
  epsilon=.1;
  sway_radius = radius; // for now.
  sway_offset = (wood_width() + double_gutter()) / (sway_far ? 1 : 2);
  sway_angle = acos(1 - ((sway_offset/2)/sway_radius)); // in degrees
  sway_length = 2 * sway_radius * sin(sway_angle);
  stub_length = (straight_length(radius) - sway_length)/2;
  stub_offset = ((offset*2)-1) * stub_length;
  if (stub_length < 0) echo("WARNING: negative stub length: ", stub_length);

  if (part=="all") {
    difference() {
      union() {
        dbl_sway60_left(radius, surface, "body", sway_far, offset,
                        mirror_connector=mirror_connector);
        dbl_sway60_left(radius, surface, "gutter", sway_far, offset);
      }
      dbl_sway60_left(radius, surface, "hole", sway_far, offset);
      dbl_sway60_left(radius, surface, "connector", sway_far, offset,
                      mirror_connector=mirror_connector);
      dbl_sway60_left(radius, surface, "ties", sway_far, offset, trim_ties=false);
    }
  } else if (part=="ties" && trim_ties) {
    intersection() {
      with_bogus60(radius)
        dbl_sway60_left(radius, surface=surface, part="ties",
                        sway_far=sway_far, offset=offset, trim_ties=false);
      dbl_sway60_left(radius, surface=surface, part="body",
                      sway_far=sway_far, offset=offset);
    }
  } else if (part=="gutter") {
    trim_gutter60(radius, surface) {
      dbl_sway60_left(radius, surface=surface, part="gutter-body",
                      sway_far=sway_far, offset=offset);
      dbl_sway60_left(radius, surface=surface, part="body",
                      sway_far=sway_far, offset=offset);
    }
  } else if (part=="gutter-body") {
    dbl_straight60(radius, surface=surface, part="gutter-body");
  } else if (part=="connector" || part=="body") {
    if (part=="body") {
      dbl_sway60_left(radius, surface, "body-main",
                      sway_far, offset);
    }
    // Bottom connector: dbl if sway_far, else normal
    suppress_body = (part=="body" && !mirror_connector);
    translate([0,-straight_length(radius)/2,0]) {
      if (sway_far) {
        if (!suppress_body)
          dbl_connector(surface=surface, part=part, mirror=mirror_connector);
      } else if (part=="connector") {
        loose_wood_cutout();
      }
    }
    // Top connector
    translate([0,straight_length(radius)/2,0]) rotate([0,0,180])
      if (!suppress_body)
        dbl_connector(surface=surface, part=part, mirror=mirror_connector);
  } else {
    translate([sway_far ? 0 : (-sway_offset/2),stub_offset,0])
      for(i=[-1,1]) rotate([0,0,(i+1)*90])
      translate([sway_offset/2,-(straight_length(radius)/2)+(i*stub_offset),0]) {
      if (part=="body-main") {
        translate([wood_width()/2,0,0])
          rotate([0,0,90]) wood_track(stub_length + (i*stub_offset) + epsilon, false);
        translate([-sway_radius,stub_length + (i*stub_offset),0])
          wood_track_arc(sway_radius - (wood_width()/2), sway_angle + epsilon,
                        false);
      } else if (part=="body-well") {
        translate([-wood_well_spacing()/2,0,0])
          cube([wood_well_spacing(), stub_length + (i*stub_offset) + epsilon,
                wood_height()]);
        translate([-sway_radius,stub_length + (i*stub_offset),0])
          ring(sway_radius, sway_angle + epsilon, wood_height(),
               wood_well_spacing());
      } else if (part=="hole" || part=="ties") {
        do_rails_or_roads(surface=surface, part=part, mirror_symmetric=false) {
          /* rails */
          for (which=["rails","ties"]) {
            which_height = (which=="rails" ? 0 : -well_tie_height());
            difference() {
              with_bogus60(radius) {
                if (part=="hole") {
                  translate([wood_width()/2, -epsilon, which_height])
                    rotate([0,0,90])
                    wood_rails(stub_length + (i*stub_offset) + 2*epsilon, bevel_ends=false);
                  translate([-sway_radius, stub_length + (i*stub_offset), which_height])
                    wood_rails_arc(sway_radius - (wood_width()/2),
                                   sway_angle + epsilon, bevel_ends=false);
                }
                if (part=="ties" && which=="ties") {
                  translate([-wood_width()/2 - sway_offset/2 - epsilon,
                             -epsilon,
                             wood_height() - tie_height()]) {
                    cube([wood_width() + (sway_offset/2) + 2*epsilon,
                          straight_length(radius)/2 +
                          (i*stub_offset) +
                          tie_width()/2 + 2*epsilon,
                          wood_height()]);
                  }
                }
              }
              if (which=="ties") {
                /* cut out ties. */
                spacing = tie_spacing(radius);
                num=ceil((straight_length(radius)/2)/spacing);
                extra=ceil((i*stub_offset)/spacing);
                for (j = [-num:1:(extra+1)] ) {
                  ypos = (straight_length(radius)/2) + (j*spacing);
                  translate([0,ypos,wood_height()])
                    cube([2*(wood_width()+sway_offset),
                          spacing - tie_width(),
                          2*wood_height()], center=true);
                }
              }
            }
          }
          /* roads */
          for (which=["road","stripe"]) {
            which_width = (which=="road") ? road_width() : stripe_width();
            which_height = road_height() -
              (which=="road" ? 0 : stripe_height());
            difference() {
              union() {
                translate([-which_width/2, -epsilon, which_height])
                  cube([which_width, stub_length + (i*stub_offset) + 2*epsilon, wood_height()]);
                translate([-sway_radius, stub_length + (i*stub_offset), which_height])
                  difference() {
                    pie(sway_radius + which_width/2, sway_angle + epsilon,
                        wood_height());
                    translate([0,0,-epsilon])
                      pie(sway_radius - which_width/2, sway_angle + 3*epsilon,
                          wood_height() + 2*epsilon, -epsilon);
                  }
              }
              if (which=="stripe") {
                /* cut out stripes */
                spacing = tie_spacing(radius)*2;
                num=ceil((straight_length(radius)/spacing)/2);
                extra=ceil((i*stub_offset)/spacing);
                for (j = [-num:1:(extra+1)] ) {
                  ypos = (straight_length(radius)/2) + (j*spacing);
                  translate([0,ypos,wood_height()])
                    cube([wood_width()+sway_offset,spacing/2, 2*wood_height()],
                          center=true);
                }
              }
            }
          }
        }
      }
    }
  }
}

module dbl_curve_sway60(radius, dir, surface="road-rail", part="all",
                        just_curve=false, far_side=false,
                        trim_ties=true) {
  if (dir=="right") {
    dbl_curve_sway60_right(radius, surface, part, just_curve, far_side,
                           trim_ties);
  } else if (dir=="left") {
    dbl_curve_sway60_left(radius, surface, part, just_curve, far_side,
                          trim_ties);
  } else { echo("bad direction", dir); }
}

module dbl_curve_sway60_right(radius, surface="road-rail", part="all",
                              just_curve=false, far_side=false,
                              trim_ties=true) {
  scale([-1,1,1])
    dbl_curve_sway60_left(radius, surface, part, just_curve, far_side,
                          trim_ties, mirror_connector=true);
}

module dbl_curve_sway60_left(radius, surface="road-rail", part="all",
                             just_curve=false, far_side=false,
                             trim_ties=true, mirror_connector=false) {
  epsilon=.1;
  if (part=="all") {
    difference() {
      union() {
        dbl_curve_sway60_left(radius, surface, "body",
                              just_curve, far_side,
                              mirror_connector=mirror_connector);
        dbl_curve_sway60_left(radius, surface, "gutter",
                              just_curve, far_side,
                              mirror_connector=mirror_connector);
      }
      dbl_curve_sway60_left(radius, surface, "hole",
                            just_curve, far_side);
      dbl_curve_sway60_left(radius, surface, "connector",
                            just_curve, far_side,
                            mirror_connector=mirror_connector);
      dbl_curve_sway60_left(radius, surface, "ties",
                            just_curve, far_side, trim_ties=false);
    }
  } else if (part=="ties" && trim_ties) {
    intersection() {
      with_bogus60(radius)
        dbl_curve_sway60_left(radius, surface=surface, part="ties",
                              just_curve=just_curve, far_side=far_side,
                              trim_ties=false);
      dbl_curve_sway60_left(radius, surface=surface, part="body",
                            just_curve=just_curve, far_side=far_side);
    }
  } else if (part=="gutter") {
    trim_gutter60(radius, surface) {
      dbl_curve_sway60_left(radius, surface=surface, part="gutter-body",
                            just_curve=just_curve, far_side=far_side);
      dbl_curve_sway60_left(radius, surface=surface, part="body",
                            just_curve=just_curve, far_side=far_side);
    }
  } else if (part=="gutter-body") {
    dbl_curve60(radius, dir="left", surface=surface, part="gutter-body");
    // Add a bit extra to connect to far_side curve (otherwise there
    // is a small gap, because far_side curve starts with straight segment)
    if (far_side) {
      translate([0,-straight_length(radius)/4,wood_height()/2])
        cube([double_gutter(),straight_length(radius)/2,wood_height()],
             center=true);
    } else {
      // extra for smooth transition on near side curve
      curve60(radius, "left", surface, "body");
    }
  } else {
    offset = (wood_width() + double_gutter())/2;
    new_radius = radius - 2*offset;
    far_offset = far_side ? (wood_width() + double_gutter())/sqrt(3) : 0;
    if (part=="connector") {
      rotate([0,0,-120]) translate([0,-straight_length(radius)/2,0])
        loose_wood_cutout();
    }
    if (!just_curve) {
      suppress = (part=="body") && (far_side != mirror_connector);
      translate([0,-straight_length(radius)/2,0]) if (!suppress)
        dbl_connector(surface=surface, part=part, mirror=mirror_connector);
    }
    translate([(far_side?1:-1)*(wood_width()+double_gutter())/2,-straight_length(radius)/2,0]) {
      if (part=="body") {
        if (!just_curve) {
          translate([wood_width()/2,0,0]) rotate([0,0,90])
            wood_track(offset*sqrt(3) - far_offset + epsilon, false);
        }
        translate([-new_radius,offset*sqrt(3) - far_offset,0]) {
          wood_track_arc(new_radius - (wood_width()/2), 60, false);
          rotate([0,0,60])
            translate([wood_width()/2+new_radius,-epsilon,0]) rotate([0,0,90])
              if (far_side) wood_track(2*far_offset + epsilon, false);
        }
      } else if (part=="body-well") {
        if (!just_curve) {
          translate([-wood_well_spacing()/2,0,0])
            cube([wood_well_spacing(), offset*sqrt(3) - far_offset + epsilon,
                  wood_height()]);
        }
        translate([-new_radius,offset*sqrt(3) - far_offset,0]) {
          ring(new_radius, 60, wood_height(), wood_well_spacing());
          rotate([0,0,60])
            translate([-wood_well_spacing()/2+new_radius,-epsilon,0])
              if (far_side)
                cube([wood_well_spacing(), 2*far_offset + epsilon,
                      wood_height()]);
        }
      } else if (part=="hole" || part=="ties") {
        do_rails_or_roads(surface=surface, part=part, mirror_symmetric=false) {
          /* rails */
          for (which=["rails","ties"]) {
            which_height = (which=="rails" ? 0 : -well_tie_height());
            difference() {
              with_bogus60(radius) {
                if (part=="hole") {
                  if (!just_curve)
                    translate([wood_width()/2, 0, which_height])
                    rotate([0,0,90])
                    wood_rails(offset*sqrt(3) - far_offset + epsilon, bevel_ends=false);
                  translate([-new_radius,offset*sqrt(3) - far_offset, which_height]) {
                    wood_rails_arc(new_radius - (wood_width()/2), 60, bevel_ends=false);
                    if (far_side) rotate([0,0,60])
                      translate([wood_width()/2+new_radius,-epsilon,0])
                      rotate([0,0,90])
                      wood_rails(2*far_offset + epsilon, false);
                  }
                }
                if (part=="ties" && which=="ties") {
                  translate([-radius+(far_side ? -offset : offset), 0,
                             wood_height() - tie_height()])
                    cube([radius + 2*offset, radius, wood_height()]);
                }
              }
              if (which=="ties") {
                /* cut out ties */
                angle = 60;
                angle_increment = tie_angle(arc_radius=radius, basic_radius=radius);
                num=ceil((angle/angle_increment)/2);
                tie_angle = 180 * tie_width() / (PI * radius);
                for (j = [-num:1:num]) {
                  translate([-radius+(far_side ? -offset : offset), 0,
                             wood_height()])
                    pie_centered(radius + wood_width() + double_gutter(),
                                 angle_increment - tie_angle,
                                 2*wood_height(),
                                 (angle/2)+((j-.5)*angle_increment) + (tie_angle/2));
                }
              }
            }
          }
          /* roads */
          for (which=["road","stripe"]) {
            which_width = (which=="road") ? road_width() : stripe_width();
            which_height = road_height() -
              (which=="road" ? 0 : stripe_height());
            difference() {
              union() {
                if (!just_curve)
                  translate([-which_width/2, -epsilon, which_height])
                    cube([which_width,
                          offset*sqrt(3) - far_offset + 2*epsilon,
                          wood_height()]);
                translate([-new_radius,offset*sqrt(3) - far_offset, which_height]) {
                  difference() {
                    pie(new_radius + which_width/2, 60 + epsilon, wood_height());
                    translate([0,0,-epsilon])
                      pie(new_radius - which_width/2, 60 + 3*epsilon,
                          wood_height() + 2*epsilon, -epsilon);
                  }
                  if (far_side) rotate([0,0,60])
                    translate([new_radius - which_width/2,-epsilon,0])
                      cube([which_width, 2*far_offset + 2*epsilon,
                            wood_height()]);
                }
              }
              if (which=="stripe") {
                /* cut out stripes */
                angle = 60;
                angle_increment = tie_angle(arc_radius=radius, basic_radius=radius)*2;
                num=ceil((angle/angle_increment)/2);
                for (j = [-num:1:num]) {
                  translate([-radius+(far_side ? -offset : offset), 0,
                             wood_height()])
                    pie_centered(radius + wood_width() + double_gutter(),
                                 angle_increment/2,
                                 2*wood_height() + epsilon,
                                 (angle/2)+((j-.25)*angle_increment));
                }
              }

            }
          }
        }
      }
    }
  }
}

module do_rails_or_roads(surface="road-rail", part="both", matrix=undef, mirror_symmetric=true) {
  if (startswith(surface, "rail-")) { children(0); /* rail on top */ }
  if (startswith(surface, "road-")) {
    if (part != "ties") children(1); /* road on top */
  }

  m = matrix != undef ? matrix :
    (trans_mat([0,0,wood_height()/2]) *
     (mirror_symmetric ? rotate_mat([0, 180, 180]) : scale_mat([1,1,-1])) *
     trans_mat([0,0,-wood_height()/2]));

  multmatrix(m) {
    if (endswith(surface, "-rail")) { children(0); /* rail on bottom */ }
    if (endswith(surface, "-road")) {
      if (part != "ties") children(1); /* road on bottom */
    }
  }
}

module loose_wood_cutout(extra_trim=0, cutout_width=undef) {
  rotate([0,0,90]) wood_cutout();
  // shorten the pieces slightly to make them fit less tightly
  trim=1;//mm
  width = (cutout_width!=undef) ? cutout_width :
    wood_width() + double_gutter() + extra_trim + trim;
  cube([width, trim, 2*wood_height()+trim], center=true);
}

// Based on wood_plug from tracklib.scad, just with the neck shifted over
// to make it deliberately incompat w/ standard plug.  This keeps kids
// from connecting single track to double track.
module dbl_wood_plug(height=wood_height()) {
  neck_length = wood_plug_neck_length();
  post_w = 6.5; // was 6
  bevel_width = 1;
  epsilon = .1;
  neck_offset = wood_plug_radius() - post_w/2 - 0.5; // was 0

  translate([-epsilon,-post_w/2 - neck_offset,0]) hull() {
    translate([0,0,1])
      cube([epsilon+neck_length,post_w,height-2]);
    translate([0,1,0])
      cube([epsilon+neck_length,post_w-2,height]);
  }
  translate([neck_length,0,0]) hull() {
    translate([0,0,1])
      cylinder(h=height-2, r=wood_plug_radius());
    cylinder(h=height, r=wood_plug_radius()-bevel_width);
  }
}

// Based on wood_cutout() from tracklib, but altered like dbl_wood_plug() is
module dbl_wood_cutout(height=wood_height()) {
  radius = wood_plug_radius() + .3;
  post_w = 6.5; // was 6
  neck_width = post_w + 1.5;
  neck_offset = wood_plug_radius() - post_w/2 - 0.5; // was 0
  neck_length = wood_plug_neck_length();
  track_height = height;
  epsilon = .1;
  bevel_width = 1;
  bevel = epsilon + bevel_width;
  bevel_pad = sqrt(.5)*(epsilon/2);
  bevel_height = sqrt(.5)*(bevel_width+epsilon);
  bevel_radius = bevel_height - bevel_pad;
  height_pad = sqrt(.5)*(bevel_width/2);

  union() {
    translate([-epsilon,-neck_width/2 - neck_offset,-epsilon]) {
      cube(size=[epsilon+neck_length,neck_width,track_height+2*epsilon]);
    }
    translate([neck_length,0,track_height/2]) {
      cylinder(h=track_height+2*epsilon,r=radius, center=true);
    }
    // bevelled edges
    translate([neck_length,0,track_height+epsilon-height_pad]) {
      cylinder(h=bevel_height+epsilon,r1=radius-bevel_pad, r2=radius+bevel_radius, center=true);
    }
    translate([neck_length,0,height_pad-epsilon]) {
      cylinder(h=bevel_height+epsilon,r1=radius+bevel_radius,r2=radius-bevel_pad, center=true);
    }
    for (i=[ (neck_width/2)-bevel_pad, -(neck_width/2)+bevel_pad ]) {
      for (j=[ track_height+bevel_pad, -bevel_pad ]) {
        translate([(neck_length-epsilon)/2,i - neck_offset,j]) {
          rotate([45,0,0]) {
            cube([epsilon+neck_length,bevel,bevel], center=true);
          }
        }
      }
    }
  }
}

// adapt traditional brio connector to new dbl_connector
// this just helps me adapt some existing track I'd made; you shouldn't need
// this for new pieces.
module dbl_dogbone(surface="road-rail") {
  offsets = surface_offsets(surface);
  offset_top = offsets[0];
  offset_bottom = offsets[1];
  height = wood_height() - offset_top - offset_bottom;
  epsilon = .1;

  old_post_w = 6;
  new_post_w = 6.5;
  neck_offset = 2.25; // copied from dbl_wood_plug, etc.

  difference() {
    union() {
      translate([(wood_width()+double_gutter())/2,0,0])
        dbl_connector(surface=surface, part="body");
      translate([0,0,offset_bottom]) scale([1,1,height/wood_height()])
        rotate([0,0,90]) wood_plug(true);
    }
    linear_extrude(height=2*wood_height()+epsilon, center=true)
      polygon(points=[
         [-old_post_w/2, 0],
         [-old_post_w/2 - new_post_w, -new_post_w],
         [-old_post_w/2 - new_post_w, 1],
         [-old_post_w/2, 1]
         ]);
    linear_extrude(height=2*wood_height()+epsilon, center=true)
      polygon(points=[
         [new_post_w/2 - neck_offset, 0],
         [new_post_w/2 - neck_offset + old_post_w, old_post_w],
         [new_post_w/2 - neck_offset + old_post_w, -1],
         [new_post_w/2 - neck_offset, -1]
         ]);
  }
}

module dbl_dogbone_plug(surface="road-rail") {
  offsets = surface_offsets(surface);
  offset_top = offsets[0];
  offset_bottom = offsets[1];
  height = wood_height() - offset_top - offset_bottom;
  length = 50; // arbitrary
  epsilon=.1;
  //$fn=8;

  scale([1,1,height/wood_height()])
  difference() {
    difference() {
      translate([-wood_width()/2, 0, 0])
        cube([wood_width(), length, wood_height()]);
      translate([-(wood_width()+double_gutter())/2,0,0])
        dbl_connector(surface="rail-rail", part="connector");
    }
    minkowski() {
      difference() {
        translate([-wood_width()/2, 0, 0])
          cube([wood_width(), length, wood_height()]);
        loose_wood_cutout();
      }
      // subtract some extra clearance
      cylinder(r=0.2, h=5, center=true, $fn=8);
    }
  }
}

// the squeeze_hack adds normal wood_cutouts that you can glue a dbl_dogbone
// into: that lets you squeeze the largest pieces onto a just-a-touch-too-small
// printer bed.  Not generally used.
module dbl_connector(surface="road-rail", part="all", mirror=false, squeeze_hack=false) {
  offsets = surface_offsets(surface);
  offset_top = offsets[0];
  offset_bottom = offsets[1];
  height = wood_height() - offset_top - offset_bottom;

  scale([mirror?-1:1,1,1])
  if (part=="connector") {
    translate([(wood_width() + double_gutter())/2,0,offset_bottom])
      rotate([0,0,90]) dbl_wood_cutout(height=height);
    // extra "looseness", like loose_wood_cutout
    trim = 1;
    difference() {
      translate([0, 0, wood_height()/2])
        cube([2*wood_width() + double_gutter() + trim, trim,
              wood_height()+trim], center=true);
      translate([-(wood_width() + double_gutter())/2, trim, offset_bottom])
        if (!squeeze_hack)
        rotate([0,0,-90]) dbl_wood_plug(height=height);
    }
    if (squeeze_hack) {
      translate([-(wood_width() + double_gutter())/2, 0, offset_bottom])
        loose_wood_cutout();
    }
  } else if (part=="body" && !squeeze_hack) {
    translate([-(wood_width() + double_gutter())/2,0,offset_bottom])
      rotate([0,0,-90]) dbl_wood_plug(height=height);
  }
}

module pie_centered(radius, angle, height, spin=0) {
  translate([0,0,-height/2]) pie(radius, angle, height, spin=spin);
}

module ring(radius, angle, height, width, spin=0, center=false) {
  epsilon=.1;
  translate([0,0,center?(-height/2):0]) rotate([0,0,spin]) difference() {
    pie(radius + width/2, angle, height);
    translate([-epsilon,0,-epsilon])
      pie(radius - width/2 + epsilon, angle + 2*epsilon, height + 2*epsilon, -epsilon);
  }
}

// a rectangle, tapered at 45 degree angles.  sort of line a cone($fn=4),
// but not just for squares.
module rect45(x, y, h, x_only=false, y_only=false) {
  intersection() {
    if (!y_only) rotate([90,0,0])
      linear_extrude(height=y, center=true)
        polygon(points=[[-x/2,0],[0,x/2],[x/2,0]]);
    if (!x_only) rotate([0,-90,0])
      linear_extrude(height=x, center=true)
        polygon(points=[[0,-y/2],[y/2,0],[0,y/2]]);
    translate([-x/2,-y/2,0])
      cube([x, y, h]);
  }
}

module dbl_roundabout60(radius, part="outer", surface="rail-blank") {
  is_outer = (part=="outer");
  inner_part =
    (part=="inner-dbl_straight") ? ")(" :
    (part=="inner-straight") ? "A/" :
    ")(A/"; // "inner-crossing"
  ring=dbl_roundabout_ring(); // dbl female connector allows a narrower ring
  nsurface = str(split(surface, "-")[0], "-blank");
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
